MatthiasWM/NewtonROMReader/otg.cpp

/*
 * In this file in this order:
 * - usbhost.cpp
 * - ff.cpp
 */


#include "otg.h"

// ==== otg.cpp ==========================================================

int uhgogo;

char otgbufrd[512];
char otgbufwr[512];
void otgfill(char *buf, int pat);
int otgBlRead(int slot, int block, int pat);
int otgBlWrite(int slot,int block, int pat);
int otgBlTest(int slot, int n);
extern char otgbufrd[512];
extern char otgbufwr[512];

#ifdef USEFATFS
FATFS fatfs;
void otgFsRead(char *fname);
void otgFsWrite(char *s);
void otgFsLs(char *s);
#endif // USEFATFS

//  cmdServer()
//  read a command from Rs232
//  execute the command

extern void (*gpf_isr)(void);
#define CMDLINEFULL 80
char cmdline[CMDLINEFULL+2];
int cmdlinepp;
void
cmdServer()
{ char *s= cmdline;
  int i, j;
  if (cmdlinepp==0) memset(cmdline, 0, sizeof(cmdline));
  if (Serial.available()>0){
    i= Serial.read();
    if ((i>=' ')&& (cmdlinepp < CMDLINEFULL))
      cmdline[cmdlinepp++]= i;
    if ((i=='\n') && (cmdlinepp>0))
      cmdlinepp= CMDLINEFULL;
  }
  if (cmdlinepp< CMDLINEFULL)
    return;         // and loop
  printf("> %s\n", cmdline);
  cmdlinepp= 0;

  if (strcmp(s, "go")==0){        // go
    printf("start uh server\n");
    uhgogo= 1;
    return;
  }
  if (strncmp(s, "v=", 2)==0){        // v= <verbose>
    i= strtol(s+2, 0, 10);
    uhstate.verbose= i;
    printf("verbose=%d\n", i);
    return;
  }
  if (strncmp(s, "blrd ", 5)==0){       // blrd <lba>
    i= strtol(s+5, &s, 10);
    j= strtol(s, 0, 16);
    otgBlRead(0, i, j<=0? -1: j);
    return;
  }
  if (strncmp(s, "blwr ", 5)==0){       // blwr <lba> <pat>
    i= strtol(s+5, &s, 10);
    j= strtol(s, 0, 16);
    otgBlWrite(0, i, j);
    return;
  }
  if (strncmp(s, "bltst", 5)==0){       // bltst <cnt>
    i= strtol(s+5, &s, 10);
    otgBlTest(0, i);
    return;
  }
  if (strcmp(s, "u")==0){         // u
    uhDump();
    return;
  }
#ifdef USEFATFS
  if (strcmp(s, "ls")==0){        // ls
    otgFsLs(s+3);
    return;
  }
  if (strncmp(s, "rd ", 3)==0){       // rd <filename>
    otgFsRead(s+3);
    return;
  }
  if (strncmp(s, "wr ", 3)==0){     // wr <filename> <n> <pat>
    otgFsWrite(s+3);
    return;
  }
#endif // USEFATFS
  printf("ERROR unknown cmd <%s>\n", cmdline);
}


#define VERBOSE1 if (uhstate.verbose)
#define VERBOSE2 if (uhstate.verbose>1)

void
uhServer()
{ static u64 t0init;      // no more than 1 per 2s
  static int ostat= UHSTAT_NULL;
  static int fs=0;
  int st;
  if (ostat== UHSTAT_NULL)
    uhInit();     // init driver
  st= uhstate.state;
  if (st<UHSTAT_DEV)
    t0init= 0;
  if (st!=ostat)        // stat changed
    VERBOSE1 uhPrintState();
  if ((st>=UHSTAT_DEV) && (st<UHSTAT_READY) && ((millis()-t0init)>2000)){
    uhInit();     // silent
    fs= 0;
  t0init= millis();
  }
  if ((st>= UHSTAT_READY)&& (fs==0)){
#ifdef USEFATFS
    memset (&fatfs, 0, sizeof(fatfs));
    f_mount(0, &fatfs);
#endif // USEFATFS
    fs= 1;
  }
  ostat= st;
}


//   pattern  -2  no compare, no dump
//    -1  no compare, dump
//    0.. compare, dump if error
//   return <0  error
//      0 rd ok, compare error
//      >0  ok, compare ok
//      
void
otgfill(char *buf, int pat)
{ int i;
  for (i=0; i<512; i++, buf++)
    *buf= pat++;
}

int
otgBlRead(int slot, int block, int pat)
{ 
  (void)slot;
  int i;
  VERBOSE1 if (pat!=-2) printf("read %d %0x\n", block, pat==-1? 0: pat);
  otgfill(otgbufwr, pat);
  if ((i= mscReadBlock(block, otgbufrd))< 0){
    printf("read failed %d\n", i);
    return i;
  }
  if (memcmp(otgbufrd, otgbufwr, 512)==0){
    return 1;
  }
  if (pat>=0)
    printf("read %d %0x compare failed\n", block, pat);
  if (pat!=-2)
    dumphex(otgbufrd, 0, 512);
  if (pat>=0){
    printf("pattern: %d %d\n", block, pat);
    dumphex(otgbufwr, 0, 512);
  }
  return 0;
}


int
otgBlWrite(int slot,int block, int pat)
{ 
  (void)slot;
  int i;
  VERBOSE1 printf("write %d %0x\n", block, pat);
  otgfill(otgbufwr, pat);
  if ((i= mscWriteBlock( block, otgbufwr))!= 0){
    printf("write failed %d\n", i);
    return 0;
  }
  return 1;
}

const int otgdt[]= { 13,0x55, 177,0x33, 1333,0x12,  117,0x00, 888,0x88, 300, 0x33,
         73,0xCC, 155,0xAF, 1404,0xE2, 1488,0x99, 999,0xFF, 257, 0xA5,
    0 };
int
otgBlTest(int slot, int n)
{ const int *p;
  if (n<1) n=1;
  for (;n>0; n--){
    for (p= otgdt; *p>0; p+=2 )
      if (otgBlWrite(slot, *p, p[1]+n)==0)
        return 0;
    for (p= otgdt; *p>0; p+=2 )
      if (otgBlRead(slot, *p, p[1]+n)==0)
        return 0;
  }
  printf("Test finished ok\n");
  return 1;
}

#ifdef USEFATFS

void
otgFsLs(char *s)
{ DIR dir; int i; char at;
  FILINFO fin;
  char lfn[_MAX_LFN+1];
#if _USE_LFN
  fin.lfname= lfn;
  fin.lfsize= sizeof(lfn);
#endif
  if ((i=f_opendir(&dir, "/"))!=0){
    printf("ERROR f_opendir %d\n", i);
    return;
  }
  for (i=0; i<100; i++){
    memset(lfn, 0, sizeof(lfn));
    if (f_readdir(&dir, &fin)!=0)
      break;
    if (fin.fname[0]==0) break;   // problem f_readdir() !
    if (lfn[0]!=0)
      printf("< %-20s", lfn);
    else
      printf("< %-20s", fin.fname);
    at=' ';
    if (fin.fattrib&AM_DIR) at='/';
    printf(" %c %d\n", at, fin.fsize);
  }
  
}

void
otgFsRead(char *fname)
{ int i;
  FIL fd;
  char buf[80];
  if ((i=f_open(&fd, fname, FA_READ))!=0){
    printf("ERROR f_open <%s> %d\n", fname, i);
    return;
  }
  while (f_gets( buf, sizeof(buf), &fd)!=0){
    printf("< %s", buf);
  }
  printf("\nEOF\n", buf);
  f_close(&fd);
}

void
otgFsWrite(char *s)
{ int i, lmax;
  FIL fd;
  char *fname=s;
  char buf[80];
  while (*s>' ') s++;
  if (*s!=0) *s++= 0;
  lmax= strtol(s, &s, 10);
  while (*s==' ') s++;
  if (lmax<=0) lmax=10;
  if ((i=f_open(&fd, fname, FA_WRITE|FA_CREATE_ALWAYS))!=0){
    printf("ERROR f_open <%s> %d\n", fname, i);
    return;
  }
  for (i=1; i<= lmax; i++){
    sprintf(buf,"line %d ", i);
    f_puts(buf, &fd);
    f_puts(s, &fd);
    f_puts("\n", &fd);
  }
  f_close(&fd);
  printf("write %s %d lines done\n", fname, lmax);
}

#endif // USEFATFS

// +++ usbhost() driver integration

void
uhStatServer()        // display stat on LED
{
#if 0
  if (uhstate.state>= UHSTAT_READY)
    digitalWrite(13, HIGH);   // turn led on
  else  digitalWrite(13, LOW);    // turn led off
          PIOA->PIO_CODR= LEDBIT2;
  else  PIOA->PIO_SODR= LEDBIT2;
#endif
}

void
uhWaitMs(int n)
{
  uhStatServer();
  delay(n);
  uhStatServer();
}

void
uhSwitch()
{
  uhStatServer();
//  switch to other task
  uhStatServer();
}

#ifdef USEFATFS
#
// +++ fatfs integration

struct billstime {
  u32 sec:5,    // seconds/2 0-29
    min: 6,   // minutes 0-59
    hour: 5,  // hour 0-23 (gmt)
    day:5,    // dd 1-31
    month: 4, // MM 1-12
    year: 7;  // yyyy-1980
};

DWORD
get_fattime()
{ union {
    DWORD d;
    struct billstime b;
  } u;
  u.d= 0;
  u.b.year= 2017-1980;
  u.b.month= 7;
  u.b.day= 24;
  u.b.hour= 16;
  u.b.min= 44;
  return u.d;
}

#if _USE_LFN
WCHAR
ff_convert(WCHAR x, UINT mode)
{ return x;
}

WCHAR
ff_wtoupper(WCHAR x)
{ return x;
}
#endif // _USE_LFN

// +++ fatfs -> usbhost interface

//  ff -> usbhost interface

DSTATUS
disk_initialize (BYTE lun)
{
  if (uhstate.state== UHSTAT_READY)
    return RES_OK;
  return RES_ERROR;
}

DSTATUS
disk_status (BYTE lun)
{
  if (uhstate.state== UHSTAT_READY)
    return RES_OK;
  return RES_ERROR;
}

DRESULT
disk_read (BYTE lun, BYTE *buf, DWORD lba, BYTE cnt)
{ int i;
  for (;cnt>0; lba++, buf+=512, cnt--){
    VERBOSE2 printf("disk_read lba=%d\n", lba);
    if ((i=mscReadBlock(lba, (char *)buf))<0)
      return RES_ERROR;
  }
  return RES_OK;
}

DRESULT
disk_write (BYTE lun, const BYTE *buf, DWORD lba, BYTE cnt)
{ int i;
  for (;cnt>0; lba++, buf+=512, cnt--){
    VERBOSE2 printf("disk_write lba=%d\n", lba);
    if ((i=mscWriteBlock(lba, (char *)buf))<0)
      return RES_ERROR;
  }
  return RES_OK;
}

DRESULT
disk_ioctl (BYTE lun, BYTE cmd, void* p)
{
  VERBOSE1 printf("disk_ioctl %d\n", cmd);
  switch (cmd) {
  case GET_SECTOR_SIZE:
  case GET_BLOCK_SIZE:
      * ((DWORD *)p)= 512;
      return RES_OK;
  case GET_SECTOR_COUNT:
      * ((DWORD *)p)= uhstate.capacity;
      return RES_OK;
  case CTRL_SYNC:
      return RES_OK;
  }
  VERBOSE1 printf("ERROR disk_ioctl %d\n", cmd);
  return RES_ERROR;
}

#endif // USEFATFS


// +++ suppport and debug functions

void
dumphex(const char *p, u32 addr, int cnt)
{ int i; uchar c; u32 *pp;
  const char tohex[]="0123456789ABCDEF";
  for (;cnt >0; cnt-=16, p+=16, addr+=16) {
    printf("%08X:", addr);
    for (i=0; i<16; i++){
      c= p[i];
      if ((i%4)==0)
        printf(" ");
      if (i < cnt)
        printf("%c%c", tohex[(c>>4)&0xF], tohex[c&0xF]);
      else  printf("  ");
    }
    printf(" /");
    for (i=0; i<16; i++){
      c= p[i];
      if ((i < cnt)&& (c>=' ') && (c<0x7F))
        printf("%c", c);
      else  printf(" ");
    }
    printf("/");
#if 1
    if ((((u32)p)&0x3)==0){   // 32bit alligned
      pp= (u32*) p; 
      for (i=0; i<16; i+=4, pp++)
        if (i<cnt)
          printf(" %08X", *pp);
    }
#endif
    printf("\n");
  }
}



// ==== usbhost.cpp ======================================================

/*
This code is in the public domain.
Created by Andreas Meyer controlord/at/controlord/dot/fr
Version 201712  (dec 2017)
*/

//#include "duedue.h"
//#include "usbhost.h"

void uhSetState(int i);     // only down!
void uhSetStateUp(int i);   // down or up 1
void uhSetStateXXX(int i);
const char *uhStatAsc();
void uhInit();
void uhInitx(char *s);
void uhInitPipe(int pipe, int token);
void uhInitPipeToken(int pipe, int token);
void uhInitAllocDpram();
void uhInitPeriph();
int uhInitResetUsb(int n, int inix);
int  uhInitEnum();
void uhEnumSaveDescr(u8 *d);
void uhEnumPrintDescr(u8 *d, int tlng);
int uhEnumConfig(u8 *d, int tlng);
void uhResetDevEndpointIn();
const char * uhErrorAsc(int ecode);
int uhSendPipe(int pipe, u8 *buf, int lng);
int uhReceivePipe(int pipe, u8 *buf, int lng);
extern void udd_interrupt();
void uhInterrupt();
void uhInterruptPipe(int pipe);
extern void (*gpf_isr)(void);

void mscInit();
int mscTstUnitReady();
int mscInquiry();
int mscReadCapacity();
int mscRequestSense();
int mscReceiveWrapper(int pipe, u32 stall);
int mscReadBlock(u32 lba, char *buf);
int mscWriteBlock(u32 lba, char *buf);
const char *scsi2asc(int code);
void uhDumpx(int pipe, const char *pre, int destr);

int uhStepFrom, uhStepTo;
#define VERBOSE0      // severe internal errors, "can not happen"
#define VERBOSE1 if (uhstate.verbose)
#define VERBOSE2 if (uhstate.verbose>1)
#define VERBOSE3 if (uhstate.verbose>2)

// +++  usbhost, msc,  scsi ***********

// +++ usb host + enumeration

#define UHLOG if (0) uhramlog
void uhramlog(const char *fmt, ...);      // debug support

#define UHPIPE_CTRL 0
#define UHPIPE_IN 1
#define UHPIPE_OUT  2
#define UHPIPES   10      // just for arrays
//#define UOTGHS_DPRAM  0x20180000
#define UOTGHS_DPRAM  UOTGHS_RAM_ADDR

//struct _uhstate {
//  volatile int  state;    // off, enumeration, ready
//  u32 capacity;   // total number of blocks
//  u16 idVendor;   // enumeration
//  u16 idProduct;
//  u8  vendor_id[8+1]; 
//  u8  product_id[16+1];
//  u8  product_rev[4+1];
//  u16 maxPower;
//};
struct _uhstate uhstate;
  
struct _uhx {         // internals
  struct _cnt {
    u32 sof;      // count sof events
    u32   pipeint;
    u32 connect;
    u32 disconnect;
    u32 stall;
    u32 tout;
    u32 errs[10]; // -1...
    u32 mscErrors;  // signal msc rd/wr error
  } cnt;
  u8  *uhDmaStartaddress;
  char  *fifoaddr[UHPIPES];
  int devpipein;    // device endpoint
  int devpipeout;   // device endpoint
  int devpipeoutLng;    // endpoint max package size
  u32 msctag;
  struct _it {
    volatile u32 pipe;
    volatile u32 mask;
    volatile u32 isr;
    volatile int done;  // 0=waiting for, >0: ok, <0: UHERROR_
  } it;       // uhx.it.
} uhx;

const char *
uhStatAsc()
{ switch(uhstate.state){
  case UHSTAT_NULL: return "";
  case UHSTAT_NODEV:  return "NODEV";
  case UHSTAT_DEV:  return "DEV";
  case UHSTAT_ENUM: return "ENUM";
  case UHSTAT_READY:  return "READY";
  default:    return "??? stat unknown";
  }
}

#define UHERROR_NOTREADY -1
#define UHERROR_TIMEOUT -2
#define UHERROR_STALL -3    // not really an error
#define UHERROR_REPLY -4
#define UHERROR_INTERN -5
#define UHERROR_IO -6
#define UHTIMEOUT 1000    // ms
#define UHTIMEOUTSENSER 5000    // ms senserequest  ?????

const char *uhAscErrors[]= { "notready", "timeout", "stall", "reply",
              "intern", "io"};
const char *
uhErrorAsc(int ecode)
{ switch(ecode){
  default:    return "";
  case UHERROR_NOTREADY:  return "ERROR: NOT READY";
  case UHERROR_TIMEOUT: return "ERROR: TIMEOUT";
  case UHERROR_STALL: return "ERROR: STALL";
  case UHERROR_REPLY: return "ERROR: REPLY";
  case UHERROR_INTERN:  return "ERROR: INTERN";
  case UHERROR_IO:  return "ERROR: IO";
  }
}

// usb device setup request

typedef struct _usb_request {
  u8  urRequestType;
  u8  urRequest;
  u16 urValue;
  u16 urIndex;
  u16 urLeng;
} usb_request;
#define USBREQUESTLNG 8
#define urFill(t, rq, v, ix, lng) \
  memset(&ur, 0, sizeof(ur));\
  ur.urRequestType= t; \
  ur.urRequest= rq; \
  ur.urValue= v; \
  ur.urIndex= ix; \
  ur.urLeng= lng;

// urRequestType
#define  USB_REQ_DIR_OUT  (0<<7) //!< Host to device
#define  USB_REQ_DIR_IN   (1<<7) //!< Device to host

#define  USB_REQ_TYPE_STANDARD  (0<<5) //!< Standard request
//#define  USB_REQ_TYPE_CLASS (1<<5) //!< Class-specific request
//#define  USB_REQ_TYPE_VENDOR  (2<<5) //!< Vendor-specific request

#define  USB_REQ_RECIP_DEVICE (0<<0) //!< Recipient device
//#define  USB_REQ_RECIP_INTERFACE (1<<0) //!< Recipient interface
#define  USB_REQ_RECIP_ENDPOINT  (2<<0) //!< Recipient endpoint
//#define  USB_REQ_RECIP_OTHER  (3<<0) //!< Recipient other
//#define  USB_REQ_RECIP_MASK (0x1F) //!< Mask

// urRequest
//efine USB_REQ_GET_STATUS    0
#define USB_REQ_CLEAR_FEATURE   1
//efine USB_REQ_SET_FEATURE   3
#define USB_REQ_SET_ADDRESS   5
#define USB_REQ_GET_DESCRIPTOR    6
//efine USB_REQ_SET_DESCRIPTOR    7
//efine USB_REQ_GET_CONFIGURATION 8
#define USB_REQ_SET_CONFIGURATION 9
//efine USB_REQ_GET_INTERFACE   10
//efine USB_REQ_SET_INTERFACE   11
//efine USB_REQ_SYNCH_FRAME   12

#define USB_EP_FEATURE_HALT   0 //  endpoint feature


#define USB_DT_DEVICE  1
#define USB_DT_CONFIGURATION  2
#define USB_DT_INTERFACE  4
#define USB_DT_ENDPOINT 5

//  USB device descriptor s

typedef struct _usb_devdesr{    // devioce descr
  u8  bLength;    //  0:
  u8  bDescriptorType;  //  1:
  u16 bcdUSB;     //  2:
  u8  bDeviceClass;   //  4:
  u8  bDeviceSubClass;  //  5:
  u8  bDeviceProtocol;  //  6:
  u8  bMaxPacketSize0;  //  7:
  u16 idVendor;   //  8:
  u16 idProduct;    //  A:
  u16 bcdDevice;    //  C:
  u8  iManufacturer;    //  E:
  u8  iProduct;   //  F:
  u8  iSerialNumber;    // 10:
  u8  bNumConfigurations; // 11: total: 18 bytes
} usb_devdescr;

typedef struct {      // configuration decr
  u8  bLength;
  u8  bDescriptorType;
  u16 wTotalLength;
  u8  bNumInterfaces;
  u8  bConfigurationValue;
  u8  iConfiguration;
  u8  bmAttributes;   // 0x40= self powered
  u8  bMaxPower;    // *2mA   lng=9
  u8  stuff[46];    // 23= 1 interface(9) + 2 epdescr(7)
} usb_confdescr;
#define CONFDESCRLNG 9

typedef struct {      // interface descr.
  u8  bLength;
  u8  bDescriptorType;
  u8  bInterfaceNumber;
  u8  bAlternateSetting;
  u8  bNumEndpoints;
  u8  bInterfaceClass;  // need MSC_CLASS
  u8  bInterfaceSubClass;
  u8  bInterfaceProtocol;
  u8  iInterface;
} usb_ifacedescr;

#define MSC_CLASS 0x08
#define  MSC_SUBCLASS_TRANSPARENT   0x06
#define  MSC_PROTOCOL_BULK          0x50

typedef struct {      // endpoint descr
  u8  bLength;
  u8  bDescriptorType;
  u8  bEndpointAddress;
  u8  bmAttributes;
  u8  wMaxPacketSize[2];
  u8  bInterval;
} usb_epdescr;
#define  USB_EP_DIR_IN        0x80
#define  USB_EP_DIR_OUT       0x00

#define USB_EP_TYPE_BULK 2

void
uhSetState(int i)     // only down!
{ if (i< uhstate.state)
    uhstate.state= i; 
  uhStatServer();
}

void
uhSetStateUp(int i)     // down or up 1
{ if (i< uhstate.state)
    uhstate.state= i; 
  if (i== uhstate.state+1)
    uhstate.state= i; 
  uhStatServer();
}

void
uhSetStateXXX(int i)      // set uncondiotioned (debug only)
{ uhstate.state= i; 
  uhStatServer();
}

int
uhError(int e)
{ int i;
  i= -1-e;        // -1->0 -2->1 ...
  if ((i>=0) && (i<10)) uhx.cnt.errs[i]++;
  UHLOG("error %d", e);
//  uhSetState(sowhat);
//  set last error ?;
  return e;
}

void
uhPrintState()
{ const char *speed;
  switch ((UOTGHS->UOTGHS_SR & UOTGHS_SR_SPEED_Msk)>>UOTGHS_SR_SPEED_Pos){
    case 0: speed= "full"; break;
    case 1: speed= "high"; break;
    case 2: speed= "low" ; break;
    default: speed="???" ; break;
  }
  printf("%s %s speed",
    uhStatAsc(),  speed);
  if (uhstate.verbose)
    printf(" v=%d", uhstate.verbose);
  if (uhstate.state>= UHSTAT_READY)
    printf(" vendor= %04X %s product= %04X %s curr= %dmA"
      " mem= %dGB",
    uhstate.idVendor, uhstate.vendor_id, uhstate.idProduct,
          uhstate.product_id,
          uhstate.maxPower,
    (uhstate.capacity/2000+300)/1000);
  printf("\n");
}


//  uhInit():
//  uhInitPeriph()  init usb host       -> UHSTAT_NODEV
//  wait for dev to connect         -> UHSTAT_DEV
//  uhInitEnum()  enumeration phase     -> UHSTAT_ENUM
//  mscInit()   int msc/sci interface, get device infos -> UHSTAT_READY
//
// ATmel:
//  step1 0: reset
//  step2 11: 20ms
//  step3 32: reset
//  step4 43: 100ms
//  step5 143: get device descr
//  step6 143: 20ms
//  step7 163: reset
//  step8 174: 100ms
//  step9 274: set address 
//  step10 274: 20ms
//  step11 294: new adrress, get dev descriptor

void
uhInit()
{ uhInitx((char *)""); }

void
uhInitx(char *s)
{
  uhStepFrom= strtol(s, &s, 10);
  if (*s==',') s++;
  uhStepTo= strtol(s, &s, 10);
  if (uhStepTo<=0) uhStepTo= 9999;
  uhInitAllocDpram();
  if (uhstate.state== UHSTAT_NULL){
    uhSetStateUp(UHSTAT_NODEV);   // stat _NULL -> _NODEV
    uhInitPeriph();
    u64 t0;
    for (t0=millis(); millis()< (t0+500);){
      uhSwitch();
      if (uhstate.state== UHSTAT_DEV)
        break;
    }
    VERBOSE2 printf("%s dev after %d ms\n",
      uhstate.state== UHSTAT_DEV? "": "no", (int)(millis()-t0));
  }
  if (uhStepTo<3)         // uhin ,2 -> stop
    goto end;
  if (uhstate.state== UHSTAT_DEV)
    uhInitEnum();
  if (uhStepTo<100)       // uhin ,99 -> stop
    goto end;
  if (uhstate.state== UHSTAT_ENUM)
    mscInit();
    end:
  VERBOSE2 printf("uhInit status= %d %s\n", uhstate.state,  uhStatAsc());
}

// seems to be ok (?)
//  same70: PLL=600  HCLK=300  MCK=150MHz   
//  sam3x:  PLL=168  HCLK= 84  MCK= 84
//  UPLLCK = 480 MHz
#define  USBDIV (10-1)      // UPLLCK / 10 --> 48 MHz
void
usbclkInit(int on)
{ 
  (void)on;
  volatile Pmc *pmc= PMC;
  PMC->CKGR_UCKR= CKGR_UCKR_UPLLCOUNT(0x3Fu) | CKGR_UCKR_UPLLEN;
  while ( !(PMC->PMC_SR & PMC_SR_LOCKU) );
  pmc->PMC_USB= PMC_USB_USBDIV(USBDIV)|PMC_USB_USBS; // UPLLCK /10
//  pmc->PMC_SCER= PMC_SCER_USBCLK;           // enable usb clock
  pmc->PMC_SCER= PMC_SCER_UOTGCLK;          // enable usb clock NYI ???

}

void
uhInitPeriph()
{ volatile Uotghs *usb= UOTGHS;
  u64 t0;
  VERBOSE2 printf("uhInitPeriph\n");
#define UOTGVBOF (1<<10)
  PIOB->PIO_PER= UOTGVBOF;
  PIOB->PIO_OER= UOTGVBOF;
  PIOB->PIO_SODR= UOTGVBOF;   // ext-power-> usb-power

  usb->UOTGHS_CTRL =        // host mode, unfreeze
      UOTGHS_CTRL_USBE|   // enable usb
      UOTGHS_CTRL_VBUSHWC;
//NYI perClockEnable(ID_UOTGHS, 1);
  usbclkInit(1);
//NYI NVIC_SetPriority((IRQn_Type) ID_UOTGHS, 5);
//NYI NVIC_EnableIRQ((IRQn_Type) ID_UOTGHS);
  gpf_isr=  uhInterrupt;
  usb->UOTGHS_CTRL =        // host mode, unfreeze
      UOTGHS_CTRL_USBE|   // enable usb
      UOTGHS_CTRL_VBUSHWC;
  usb->UOTGHS_HSTCTRL= 0;
  for (t0=millis()+1000; t0>millis();){
    uhSwitch();
    if (usb->UOTGHS_SR& UOTGHS_SR_CLKUSABLE)
      goto uhp1;
  }
  VERBOSE0 printf("uhInitPerph failed (clk usable)\n");
  return;
   uhp1:
  usb->UOTGHS_HSTICR= 0x7F;     // clear all it
  usb->UOTGHS_SFR = UOTGHS_SFR_VBUSRQS;   // enable vbus (must)
  usb->UOTGHS_HSTIER=
    UOTGHS_HSTIER_DCONNIES|
    UOTGHS_HSTIER_DDISCIES|
    0; //  UOTGHS_HSTIER_HSOFIES; // remove SOF ???
}

#define XX 1  // normal delay timing

// atmel reset proc step3:

int
uhInitResetUsb(int n, int inix)         // reset usb
{ volatile Uotghs *usb= UOTGHS;
  u64 t0; int ret=0;
  u32 hstier= usb->UOTGHS_HSTIMR;
  uhInitPeriph();
  UHLOG("reset usb");
  usb->UOTGHS_HSTIDR= 0xFFFFFFFF;
  usb->UOTGHS_HSTCTRL= 0;
  usb->UOTGHS_HSTCTRL= UOTGHS_HSTCTRL_RESET;  // reset usb
  for (t0=millis(); millis()<t0+ 5000;){  // 500 !!!
    uhSwitch();
    if (usb->UOTGHS_HSTISR& UOTGHS_HSTISR_RSTI)
      goto uhp2;
  }
  VERBOSE1 printf("uhInitReset failed (reset %d)\n", n);
  ret= UHERROR_NOTREADY;
    uhp2:
  VERBOSE2 printf("reset in %d ms\n", (int)(millis()-t0));
  uhWaitMs(30*XX);
  usb->UOTGHS_HSTCTRL= 0;
  usb->UOTGHS_HSTICR= UOTGHS_HSTICR_RSTIC;
  usb->UOTGHS_HSTCTRL= UOTGHS_HSTCTRL_SOFE;   // sof enable, needed!
  uhWaitMs(20*XX);
  if (inix==0)
    goto ier;
  uhWaitMs(100*XX);
  usb->UOTGHS_HSTCTRL= UOTGHS_HSTCTRL_SOFE;   // sof enable, needed!
  uhWaitMs(3*XX);
  uhInitPipe(UHPIPE_CTRL, -1);
  uhWaitMs(10*XX);
    ier:
  usb->UOTGHS_HSTICR= 0x7F;     // clear all ints
  usb->UOTGHS_HSTIER= hstier;     // restore hst int mask
  return ret;
}


int
uhInitEnum()            // uhin
{ volatile Uotghs *usb= UOTGHS;
  int i, redocnt=0, lng=100;
  usb_request ur;
  usb_devdescr udev;
  usb_confdescr uconf;
  u8 confno;
  VERBOSE2 printf("uhInitEnum\n");
  switch (uhStepFrom){
  case 5: goto step5;       // uhin 5
  case 6: goto step6;
  case 7: goto step7;
  case 13: goto step13;
  }
  uhWaitMs(50*XX);        // essentiel needs this
  if ((i=uhInitResetUsb(1, 0))<0)     // reset usb
    return i;
  if ((i=uhInitResetUsb(2, 1))<0)     // reset usb
    return i;

  usb->UOTGHS_HSTADDR1= (0<<16)|(0<<8)|(0<<0);
  if (uhStepTo<= 5) return 0;     // uhin ,5
    step5:
  VERBOSE2 printf("Step5 get dev descr\n"); // step5 get devdescr
  VERBOSE3 uhDumpx(-1, "", 1);
  UHLOG("step5 get dev descr");
  urFill( USB_REQ_RECIP_DEVICE|USB_REQ_TYPE_STANDARD|USB_REQ_DIR_IN,
    USB_REQ_GET_DESCRIPTOR, 
    USB_DT_DEVICE<<8,
    0,
    8);
  if ((i=uhSendPipe(UHPIPE_CTRL, (u8 *)&ur, USBREQUESTLNG))<0) // step5
    return i;
  if (uhStepTo<= 6) return 0;     // uhin ,6
    step6:
  if ((i=uhReceivePipe(UHPIPE_CTRL, (u8 *)&udev, sizeof(udev)))<0)
    return i;
  if (uhStepTo<= 7) return 0;     // uhin ,7

  uhWaitMs(20*XX);
    step7:
  if ((i=uhInitResetUsb(3, 1))<0)     // reset usb step7
    return i;

  VERBOSE2 printf("Step9 set addr\n");    // step9 set address
  UHLOG("step9 set addr");
  urFill( USB_REQ_RECIP_DEVICE|USB_REQ_TYPE_STANDARD|USB_REQ_DIR_OUT,
    USB_REQ_SET_ADDRESS,    // set address
    1,        // new address
    0,
    0);

  if ((i=uhSendPipe(UHPIPE_CTRL, (u8 *)&ur, USBREQUESTLNG))<0)
    return i;
  if ((i=uhReceivePipe(UHPIPE_CTRL, 0, 0))<0)
    return i;
  uhWaitMs(20*XX);

  VERBOSE2 printf("Step11 get dev descr\n");  // step11 new ad, get dev descr
  UHLOG("step11 get dev descr");
  usb->UOTGHS_HSTADDR1= (1<<16)|(1<<8)|(1<<0);
  urFill( USB_REQ_RECIP_DEVICE|USB_REQ_TYPE_STANDARD|USB_REQ_DIR_IN,
    USB_REQ_GET_DESCRIPTOR,     // get descriptor
    USB_DT_DEVICE<<8,
    0,
    sizeof(usb_devdescr));
  if ((i=uhSendPipe(UHPIPE_CTRL, (u8 *)&ur, USBREQUESTLNG))<0)
    return i;
  if ((i=uhReceivePipe(UHPIPE_CTRL, (u8 *)&udev, sizeof(udev)))<0)
    return i;
  uhEnumSaveDescr((u8 *) &udev);
  VERBOSE2 uhEnumPrintDescr((u8 *) &udev, 0);

  VERBOSE2 printf("Step12 get conf descr\n"); // step12 get config descr
  UHLOG("step12 get conf descr");
  urFill( USB_REQ_RECIP_DEVICE|USB_REQ_TYPE_STANDARD|USB_REQ_DIR_IN,
    USB_REQ_GET_DESCRIPTOR,     // get descriptor
    USB_DT_CONFIGURATION<<8,
    0,
    CONFDESCRLNG);
  if ((i=uhSendPipe(UHPIPE_CTRL, (u8 *)&ur, USBREQUESTLNG))<0)
    return i;
  if ((i=uhReceivePipe(UHPIPE_CTRL, (u8 *)&uconf, CONFDESCRLNG))<0)
    return i;
  uhEnumSaveDescr((u8 *) &uconf);
  VERBOSE2 uhEnumPrintDescr((u8 *) &uconf, 0);
  confno= 1; 
  lng= uconf.wTotalLength;

  if (uhStepTo<= 13) return 0;      // uhin ,5
    step13:
  VERBOSE2 printf("Step13 get interf descr\n"); // step13 get interf. descr
  UHLOG("step13 get interf descr");
  if (lng>(int)sizeof(uconf)) lng= sizeof(uconf);
  urFill( USB_REQ_RECIP_DEVICE|USB_REQ_TYPE_STANDARD|USB_REQ_DIR_IN,
    USB_REQ_GET_DESCRIPTOR,     // get descriptor
    USB_DT_CONFIGURATION<<8|(confno-1),
    0,
    lng);
  if ((i=uhSendPipe(UHPIPE_CTRL, (u8 *)&ur, USBREQUESTLNG))<0)
    return i;
  memset(&uconf, 0, sizeof(uconf));
  if ((i=uhReceivePipe(UHPIPE_CTRL, (u8 *)&uconf, lng))<0){
    if (++redocnt<3) goto step13;   // for the sakeOf Lexar
    return i;
  }
  VERBOSE2 uhEnumPrintDescr((u8 *) &uconf, i);
  i=uhEnumConfig((u8 *) &uconf, i);
//  verify interface & endpoint descr, set confno
//  and reinit pipes 1,2
  uhInitPipe(UHPIPE_IN, -1);
  uhInitPipe(UHPIPE_OUT, -1);
  if (i>=0){
    VERBOSE2 printf("conf interface in pipe=%d endp=%d out pipe=%d"
             " endp=%d\n",
            UHPIPE_IN, uhx.devpipein, UHPIPE_OUT, uhx.devpipeout);
  } else VERBOSE2 printf("conf interface failed\n");

  VERBOSE2 printf("Step14\n");      // step14 enable dev config
  UHLOG("step14");

  urFill( USB_REQ_RECIP_DEVICE|USB_REQ_TYPE_STANDARD|USB_REQ_DIR_OUT,
    USB_REQ_SET_CONFIGURATION,    //  set config
    confno,
    0,
    0);
  if ((i=uhSendPipe(UHPIPE_CTRL, (u8 *)&ur, USBREQUESTLNG))<0)
    return i;
  if ((i=uhReceivePipe(UHPIPE_CTRL, 0, 0))<0)
    return i;

  uhSetStateUp(UHSTAT_ENUM);
  return 0;
}

void
uhResetDevEndpointIn()      // reset device endpoint in
{ int i;
  int ep= uhx.devpipein;      // device endpoint IN
  if (ep==0) ep= UHPIPE_IN;
  ep|= 0X80;
  usb_request ur;
  urFill( USB_REQ_RECIP_ENDPOINT|USB_REQ_TYPE_STANDARD|USB_REQ_DIR_OUT,
    USB_REQ_CLEAR_FEATURE,  
    USB_EP_FEATURE_HALT,
    ep,
    0);
  if ((i=uhSendPipe(UHPIPE_CTRL, (u8 *)&ur, USBREQUESTLNG))<0)
    return;
  if ((i=uhReceivePipe(UHPIPE_CTRL, 0, 0))<0)
    return;
  return;
}

void      // save descriptor device, config, -> uhstat
uhEnumSaveDescr(u8 *d)
{ 
  usb_devdescr *udev;
  usb_confdescr *uco;
  udev= (usb_devdescr *) d;
  uco= (usb_confdescr *) d;
  switch(d[1]){
  case USB_DT_DEVICE:
    uhstate.idVendor= udev->idVendor;
    uhstate.idProduct= udev->idProduct;
    break;
  case USB_DT_CONFIGURATION:
    uhstate.maxPower= uco->bMaxPower*2;
    break;
  }
}

void      // print descriptor device, config, interface, endpoint
uhEnumPrintDescr(u8 *d, int tlng)
{ 
  usb_devdescr *udev;
  usb_confdescr *uco;
  usb_ifacedescr *id;
  usb_epdescr *ep;
  int i, lng;
  char mclass[10], subcl[10], prot[10], eptype[0];
  more:
  lng= d[0];
  udev= (usb_devdescr *) d;
  uco= (usb_confdescr *) d;
  id=  (usb_ifacedescr *) d;
  ep=  (usb_epdescr *) d;
  switch(d[1]){
  case USB_DT_DEVICE:
    printf("dev descr devClass=%X devSubClass=%X devProt=%X"
      " idVendor=%04X idProduct=%04X\n",
      udev->bDeviceClass, udev->bDeviceSubClass,
            udev->bDeviceProtocol, udev->idVendor, udev->idProduct);
    break;
  case USB_DT_CONFIGURATION:
    printf("config descr tlng=%d interf=%d curr=%dmA\n",
           uco->wTotalLength, uco->bNumInterfaces, uco->bMaxPower*2);
    break;
  case USB_DT_INTERFACE:
    switch (id->bInterfaceClass){
    case MSC_CLASS: strcpy(mclass,"msc"); break;
    default: strcpy(mclass,"");
    }
    switch (id->bInterfaceSubClass){
    case MSC_SUBCLASS_TRANSPARENT: strcpy(subcl,"transp"); break;
    default: strcpy(subcl,"");
    }
    switch (id->bInterfaceProtocol){
    case MSC_PROTOCOL_BULK: strcpy(prot,"bulk"); break;
    default: strcpy(prot,"");
    }
    printf("interface desccr no=%d endps=%d class=%X(%s)"
             " subclass=%X(%s) prot=%d(%s)\n",
      id->bInterfaceNumber, id->bNumEndpoints,
            id->bInterfaceClass, mclass, id->bInterfaceSubClass,
            subcl, id->bInterfaceProtocol, prot);
    break;

  case USB_DT_ENDPOINT:
    switch (ep->bmAttributes){
    case USB_EP_TYPE_BULK: strcpy(eptype,"bulk"); break;
    default: strcpy(eptype,"");
    }
    i= (ep->wMaxPacketSize[1]<<8)|ep->wMaxPacketSize[0];
    printf("endpoint desccr attr=%d(%s) addr=%X"
             " packagesize=%d\n",
      ep->bmAttributes, eptype, ep->bEndpointAddress, i);
    break;
  default:
    printf("descr UNKNOWN typ=%d lng=%d\n", d[1], lng);
    break;
  }
  if ((lng>0) && ((tlng-= lng)>0)){
    d+= lng;
    goto more;
  }
}

int
uhEnumConfig(u8 *d, int tlng)
{ int got=0, i;
  usb_ifacedescr *id;
  usb_epdescr *ep;
  for (;tlng>0; tlng-= d[0], d+= d[0]){
    switch(d[1]){
    case USB_DT_INTERFACE:
      id= (usb_ifacedescr *) d;
      if ((id->bInterfaceClass   == MSC_CLASS)
      && (id->bInterfaceSubClass == MSC_SUBCLASS_TRANSPARENT)
      && (id->bInterfaceProtocol == MSC_PROTOCOL_BULK) )
        got=0x4;
      break;
    case USB_DT_ENDPOINT:
      ep= (usb_epdescr *) d;
      if (got==0)
              break;
      if (ep->bmAttributes != USB_EP_TYPE_BULK)
        break;
      i= (ep->wMaxPacketSize[1]<<8)|ep->wMaxPacketSize[0];
      if (ep->bEndpointAddress & USB_EP_DIR_IN) {
        uhx.devpipein = ep->bEndpointAddress&
                    ~USB_EP_DIR_IN;
        got|= 0x2;
      } else {
        uhx.devpipeout= ep->bEndpointAddress;
        uhx.devpipeoutLng= i;
        got|= 0x1;
      }
      break;
    }
  }
  return (got==0x7? 0: -1);
}


void
uhInitPipe(int pipe, int token)
{ volatile Uotghs *usb= UOTGHS;
  u32 type, size, devep;
  switch (pipe){
  case UHPIPE_CTRL:         // default?  cc 
  default:  type= UOTGHS_HSTPIPCFG_PTYPE_CTRL;
      if (token<0)
        token=  UOTGHS_HSTPIPCFG_PTOKEN_SETUP;
      size= UOTGHS_HSTPIPCFG_PSIZE_64_BYTE;
      devep= UHPIPE_CTRL;
      break;
  case UHPIPE_IN: if (token<0)
        token=  UOTGHS_HSTPIPCFG_PTOKEN_IN;
      if ((devep= uhx.devpipein)==0)
        devep= UHPIPE_IN;
      goto ptypeblk;
  case UHPIPE_OUT: if (token<0)
        token=  UOTGHS_HSTPIPCFG_PTOKEN_OUT;
      if ((devep= uhx.devpipeout)==0)
        devep= UHPIPE_OUT;
  ptypeblk: type= UOTGHS_HSTPIPCFG_PTYPE_BLK;
      size= UOTGHS_HSTPIPCFG_PSIZE_512_BYTE;
      break;
  }

  usb->UOTGHS_HSTPIP|= UOTGHS_HSTPIP_PEN0<<pipe;    // enable
  usb->UOTGHS_HSTPIP|= UOTGHS_HSTPIP_PRST0<<pipe;   // reset 
  usb->UOTGHS_HSTIDR= (UOTGHS_HSTIDR_PEP_0<<pipe);    // disable ints
  usb->UOTGHS_HSTPIPCFG[pipe]=        // config
            UOTGHS_HSTPIPCFG_PEPNUM(devep)|
      type|
      token|
      size|
      UOTGHS_HSTPIPCFG_PBK_1_BANK|
      UOTGHS_HSTPIPCFG_ALLOC;

  usb->UOTGHS_HSTPIP&= ~(UOTGHS_HSTPIP_PRST0<<pipe);  // stop reset
  usb->UOTGHS_HSTPIPIER[pipe]=        // enable ints
      UOTGHS_HSTPIPIER_PFREEZES|
      UOTGHS_HSTPIPIER_RXSTALLDES|
      UOTGHS_HSTPIPIER_PERRES;
  usb->UOTGHS_HSTPIPICR[pipe]= 0xF7;      // ack all ints
  usb->UOTGHS_HSTIER= (UOTGHS_HSTIER_PEP_0<<pipe);    // enable ints
}

void
uhInitPipeToken(int pipe, int token)
{
  uhInitPipe(pipe, token);
}

void
uhInitAllocDpram()
{
  char *dp= (char*)UOTGHS_DPRAM;
  uhx.fifoaddr[UHPIPE_CTRL]= dp;
  dp+= 64;        // PSIZE_64 see above
  uhx.fifoaddr[UHPIPE_IN]= dp;
  dp+= 512;       // PSIZE_512 see above
  uhx.fifoaddr[UHPIPE_OUT]= dp;
}


int
uhSendPipe(int pipe, u8 *buf, int lng)
{ volatile Uotghs *usb= UOTGHS;
  u64 t0;
  int ret= 0;
  uhInitPipeToken(pipe, UOTGHS_HSTPIPCFG_PTOKEN_SETUP);
  uhx.it.pipe= pipe;
  uhx.it.mask=  UOTGHS_HSTPIPISR_TXSTPI;
  uhx.it.done= 0;
  VERBOSE2 printf("uhSendPipe pipe=%d %08X:\n", pipe, (unsigned int)uhx.fifoaddr[pipe]);
  VERBOSE2 dumphex((char *)buf, (u32)buf, lng);
  VERBOSE3 uhDumpx(0, "->fifo", 0);
  memcpy(uhx.fifoaddr[pipe], buf, lng);   // fill fifo
  usb->UOTGHS_HSTPIPICR[pipe]= 0xF7;    // ack all ints -> FIFOCON=1
  usb->UOTGHS_HSTPIPIER[pipe]= UOTGHS_HSTPIPIER_TXSTPES;  // en txstp  int
  usb->UOTGHS_HSTPIPIDR[pipe]= UOTGHS_HSTPIPIDR_FIFOCONC; // FIFOCOn=0, start 
  usb->UOTGHS_HSTPIPIDR[pipe]= UOTGHS_HSTPIPIDR_PFREEZEC; // unfreeze pipe

  for (t0=millis()+UHTIMEOUT; ;){   // wait TXOUTI
    if (uhx.it.done)
      break;
    uhSwitch();
    if (millis()>=t0){
      VERBOSE1 printf("ERROR uhSendPipe timeout\n");
      ret= uhError(UHERROR_TIMEOUT);
      break;
    }
  }
  if ((uhstate.verbose>1) && (ret==0))
    printf("uhSendPipe ok intisr=%08X isr=%08X dma=%08X lng= %d(%x)\n",
      uhx.it.isr, (unsigned int)usb->UOTGHS_HSTPIPISR[pipe],
      0, lng, lng);
  if ((uhstate.verbose>0) && (ret!=0)){
    printf("uhSendPipe ERROR intisr=%08X lng= %d(%x)\n",
    uhx.it.isr, 0, lng);
    uhDumpx(pipe,0,1);
  }
  usb->UOTGHS_HSTPIPIDR[pipe]= UOTGHS_HSTPIPIDR_TXSTPEC;  // dis txstp int
  usb->UOTGHS_HSTPIPIER[pipe]= UOTGHS_HSTPIPIER_PFREEZES; // freeze pipe
  if (uhstate.state< UHSTAT_DEV) ret= UHERROR_NOTREADY;
  return ret;
}

//
// setup pipe, receive data, copie fifo->buf

int
uhReceivePipe(int pipe, u8 *buf, int lng)
{ volatile Uotghs *usb= UOTGHS;
  u32 dlng, isr;
  u64 t0;
  int ret= 0;
  uhInitPipeToken(pipe, UOTGHS_HSTPIPCFG_PTOKEN_IN);
  uhx.it.pipe= pipe;
  uhx.it.mask=  UOTGHS_HSTPIPISR_RXINI;
  uhx.it.done=  0;
  VERBOSE2 printf("uhReceivePipe pipe=%d\n", pipe);
//  VERBOSE2 uhDumpx(0, "<-rcvP", 0);
  usb->UOTGHS_HSTPIPIER[pipe]= UOTGHS_HSTPIPIER_RXINES; // en tr empty int
  usb->UOTGHS_HSTPIPIDR[pipe]= UOTGHS_HSTPIPIDR_FIFOCONC; // FIFOCOn=0, start 
  usb->UOTGHS_HSTPIPIDR[pipe]= UOTGHS_HSTPIPIDR_PFREEZEC; // unfreeze pipe

  for (t0=millis()+UHTIMEOUT; ;){
    if ((uhx.it.done) &&
      (usb->UOTGHS_HSTPIPIMR[pipe]& UOTGHS_HSTPIPIMR_PFREEZE))
      break;
    uhSwitch();
    if (millis()>=t0){
      VERBOSE1 printf("ERROR uhReceivePipe timeout\n");
      ret= uhError(UHERROR_TIMEOUT);
      break;
    }
  }
  isr= usb->UOTGHS_HSTPIPISR[pipe];
  dlng= isr>> UOTGHS_HSTPIPISR_PBYCT_Pos;
  memset(buf, 0, lng);
  memcpy(buf, uhx.fifoaddr[pipe], dlng<lng? dlng: lng);
  if ((uhstate.verbose>0) && ((uhstate.verbose>1)||(ret!=0))){
    printf("uhReceivePipe %s lng=%d(%X) ",
      ret==0? "ok": "error", dlng, dlng);
    uhDumpx(0,0,1);
  }
  VERBOSE2 dumphex((char *)buf, (u32)buf, dlng);
  usb->UOTGHS_HSTPIPICR[pipe]= 0xF7;      // ack all ints 
  usb->UOTGHS_HSTPIPIDR[pipe]= UOTGHS_HSTPIPIDR_RXINEC; // en tr empty int
  usb->UOTGHS_HSTPIPIER[pipe]= UOTGHS_HSTPIPIER_PFREEZES; // freeze pipe
  if (uhstate.state< UHSTAT_DEV) return UHERROR_NOTREADY;
  if (ret==0) ret= dlng;
  return ret;
}

void
uhDmaSetupIn(int pipe, u8 *buf, int lng)
{ volatile Uotghs *usb= UOTGHS;
  volatile UotghsHstdma *hs= & usb->UOTGHS_HSTDMA[pipe-1];
  u32 ctrl;
  uhx.uhDmaStartaddress= buf;
  hs->UOTGHS_HSTDMANXTDSC=0;
  hs->UOTGHS_HSTDMAADDRESS= (u32)buf;
  ctrl= UOTGHS_HSTDMACONTROL_CHANN_ENB;
  hs->UOTGHS_HSTDMACONTROL= (lng<<16)| ctrl;
}

int
uhDmaSetupOut(int pipe, u8 *buf, int lng)
{ volatile Uotghs *usb= UOTGHS;
  volatile UotghsHstdma *hs= & usb->UOTGHS_HSTDMA[pipe-1];
  u32 ctrl;
  int i;
  uhx.uhDmaStartaddress= buf;
  hs->UOTGHS_HSTDMANXTDSC=0;
  hs->UOTGHS_HSTDMAADDRESS= (u32)buf;
  ctrl= UOTGHS_HSTDMACONTROL_CHANN_ENB |
    UOTGHS_HSTDMACONTROL_END_B_EN;    // -> pipe
  hs->UOTGHS_HSTDMACONTROL= (lng<<16)| ctrl;
  for (i=0; i<1000; i++)
    if (hs->UOTGHS_HSTDMAADDRESS>= ((u32)uhx.uhDmaStartaddress+lng))
      break;
  if (i>=1000){
    VERBOSE1 printf("ERROR uhDmaSetupOut send data to fifo\n");
    return -1;
  }
  return 0;
}

u32
uhDmaEnd(int pipe)      // return length of last dma transfer
{ volatile Uotghs *usb= UOTGHS;
  volatile UotghsHstdma *hs= & usb->UOTGHS_HSTDMA[pipe-1];
  return hs->UOTGHS_HSTDMAADDRESS- (u32)uhx.uhDmaStartaddress;
}

//  setup pipe, setup dma, copy data->fifo, send data
int
uhSend(int pipe, u8 *buf, int lng)
{ volatile Uotghs *usb= UOTGHS;
  u32 dlng;
  u64 t0;
  int ret= 0;
  if (uhstate.verbose>1) {
    printf("uhSend pipe=%d: ", pipe);
    if (strncmp((char *)buf, "USBC", 4)==0)
      printf("%s", scsi2asc(buf[15])); 
    printf("\n");
    dumphex((char *)buf, (u32)buf, lng);
  }
    more:
  uhx.it.pipe= pipe;
  uhx.it.mask=  UOTGHS_HSTPIPISR_TXOUTI;
  uhx.it.done= 0;
  dlng= uhx.devpipeoutLng;
  if ((dlng==0)||(dlng>lng))
    dlng= lng;
  if (uhDmaSetupOut(pipe, buf, dlng)<0){      // fill fifo
      ret= uhError(UHERROR_INTERN);
      goto ex;
  }
  usb->UOTGHS_HSTPIPICR[pipe]= 0xF7;    // ack all ints -> FIFOCON=1
  usb->UOTGHS_HSTPIPIER[pipe]= UOTGHS_HSTPIPIER_TXOUTES;  // en tr empty int
  usb->UOTGHS_HSTPIPIDR[pipe]= UOTGHS_HSTPIPIDR_PFREEZEC; // unfreeze pipe
  usb->UOTGHS_HSTPIPIDR[pipe]= UOTGHS_HSTPIPIDR_FIFOCONC; // FIFOCOn=0, start 

  for (t0=millis()+UHTIMEOUT; uhx.it.done==0;){
    uhSwitch();
    if (millis()>=t0){
      VERBOSE1 printf("ERROR uhSend timeout\n");
      ret= uhError(UHERROR_TIMEOUT);
      break;
    }
  }
  dlng= uhDmaEnd(pipe);
  if ((dlng<=0) && (ret==0)) ret= uhError(UHERROR_INTERN);
  if ((uhstate.verbose>0) && ((uhstate.verbose>1)||(ret!=0)))
    printf("uhSend %s intisr=%08X isr=%08X dma=%08X lng= %d(%x)\n",
    ret==0? "ok": "error",
    uhx.it.isr, usb->UOTGHS_HSTPIPISR[pipe], 0, dlng, dlng);
  usb->UOTGHS_HSTPIPIER[pipe]= UOTGHS_HSTPIPIER_PFREEZES; // freeze pipe
  if (uhstate.state< UHSTAT_ENUM) ret= UHERROR_NOTREADY;
  if ((ret==0) && (dlng< lng)) {        // more
    buf+= dlng;
    lng-= dlng;
    goto more;
  }
    ex:
  return ret;
}


//  setup dma, pipe, receive data

int
uhReceive(int pipe, u8 *buf, int lng, int tout)
{ volatile Uotghs *usb= UOTGHS;
  u32 dlng;
  u64 t0;
  int ret= 0;
  u8 *cbuf= buf;
  int   clng= lng;
  memset(buf, 0x33, lng);
    more:
  uhx.it.pipe= pipe;
  uhx.it.mask=  UOTGHS_HSTPIPISR_RXINI;
  uhx.it.done=  0;
  VERBOSE2 printf("uhReceive pipe=%d\n", pipe);
//  usb->UOTGHS_HSTPIPICR[pipe]= 0xF7;    // ack all ints -> FIFOCON=1
  usb->UOTGHS_HSTPIPIER[pipe]= UOTGHS_HSTPIPIER_RXINES; // en tr empty int
  usb->UOTGHS_HSTPIPIDR[pipe]= UOTGHS_HSTPIPIDR_FIFOCONC; // FIFOCOn=0, start 
  usb->UOTGHS_HSTPIPIDR[pipe]= UOTGHS_HSTPIPIDR_PFREEZEC; // unfreeze pipe
  uhDmaSetupIn(pipe, cbuf, clng);

  for (t0=millis()+ tout; uhx.it.done==0;){
    uhSwitch();
    if (millis()>=t0){
      VERBOSE1 printf("ERROR uhReceive timeout\n");
      ret= uhError(UHERROR_TIMEOUT);
      break;
    }
  }
  if (uhx.it.done<0)
    ret= uhError(uhx.it.done);      // STALL
  dlng= uhDmaEnd(pipe);
  if ((uhstate.verbose>1) ||
            ((uhstate.verbose>1)&&(ret!=0)&&(ret!=UHERROR_STALL))){
    printf("uhReceive %s lng=%d(%X) intisr= ",
          ret==0?"ok":"error", dlng,dlng, uhx.it.isr);
    uhDumpx(0,0,1);
  }
  usb->UOTGHS_HSTPIPIDR[pipe]= UOTGHS_HSTPIPIDR_RXINEC; // en tr empty int
  usb->UOTGHS_HSTPIPIER[pipe]= UOTGHS_HSTPIPIER_PFREEZES; // freeze pipe
  if (uhstate.state< UHSTAT_ENUM) ret= UHERROR_NOTREADY;
  if ((ret==0) && (dlng< clng)) {       // more
    cbuf+= dlng;
    clng-= dlng;
    goto more;
  }
  VERBOSE2 dumphex((char *)buf, (u32)buf, lng);
  return ret;
}

void
uhConnect(int present, u32 isr)
{ static  u64 otic; static int ocnt; int v;
  if ((millis()-otic)>1000) ocnt=0;   // avoid >5 msg/s
  otic= millis();
  ocnt++;
  if (present){
    uhx.cnt.connect++;
    uhSetStateUp(UHSTAT_DEV);
    if (ocnt<5){
      UHLOG("dev con %08x", isr);
      VERBOSE2 printf("dev connected\n");
    }
  } else {
    v= uhstate.verbose;
    memset(&uhstate, 0, sizeof(uhstate));
    uhstate.verbose= v;
    uhx.cnt.disconnect++;
    uhSetStateUp(UHSTAT_NODEV);
    UOTGHS->UOTGHS_HSTCTRL= 0;  // host to idle state
            // for the sakeOf Toshiba
    if (ocnt< 5){
      UHLOG("dev discon %08x", isr);
      VERBOSE2 printf("dev disconnected\n");
    }
  }
}

void
uhInterrupt()
{ volatile Uotghs *usb= UOTGHS;
  u32 pipe, isr, imr;
  uhStatServer();
  isr= UOTGHS->UOTGHS_HSTISR;
  imr = UOTGHS->UOTGHS_HSTIMR;
  pipe= ctz(((isr & imr) >> 8) | (1 << 10));
  if (isr & UOTGHS_HSTISR_HSOFI){       // sof
    usb->UOTGHS_HSTICR= UOTGHS_HSTICR_HSOFIC;
    uhx.cnt.sof++;
    return;
  }
  VERBOSE2 printf(".");
  if (imr & isr & UOTGHS_HSTISR_DDISCI){      // disconnect
    usb->UOTGHS_HSTICR= UOTGHS_HSTICR_DDISCIC |
           UOTGHS_HSTICR_DCONNIC;

    uhConnect(0, isr);
    return;
  }
  if (imr & isr & UOTGHS_HSTISR_DCONNI){      // connect
    usb->UOTGHS_HSTICR= UOTGHS_HSTICR_DCONNIC|
           UOTGHS_HSTICR_DDISCIC;
    uhConnect(1, isr);
    return;
  }
  if (pipe <10){
    uhInterruptPipe(pipe);
    uhStatServer();
    return;
  }
  printf("ERROR unexpected usb host int isr=%08X imr=%08X\n", isr, imr);
  usb->UOTGHS_HSTICR= 0x7F;
}
    
void
uhInterruptPipe(int pipe)
{ volatile Uotghs *usb= UOTGHS;
  u32 isr, imr, err, ack;
  isr= usb->UOTGHS_HSTPIPISR[pipe];
  imr= usb->UOTGHS_HSTPIPIMR[pipe];
  err= usb->UOTGHS_HSTPIPERR[pipe];
  uhx.cnt.pipeint++;
  if ((uhx.it.pipe==pipe) && ((uhx.it.mask&isr)!=0)&& (uhx.it.done==0)){
    uhx.it.done= 1;
  endpipe:
    uhx.it.isr= isr;
    UHLOG("p%d: int %X isr=%08X", pipe, isr&imr, isr);
    ack= isr&uhx.it.mask;
    usb->UOTGHS_HSTPIPICR[pipe]= ack;   // ack int
    return;
  }
  if (isr&UOTGHS_HSTPIPISR_RXSTALLDI){
    VERBOSE2 uhDumpx(pipe,"ERROR usb pipe STALL", 0); // STALL
    uhx.cnt.stall++;
    if ((uhx.it.pipe==pipe) && (uhx.it.done==0)){
      uhx.it.done= UHERROR_STALL;
      goto endpipe;
    }
  } else  VERBOSE1 uhDumpx(pipe,"ERROR unexpected usb pipe int", 0);
  if (err!=0)
    usb->UOTGHS_HSTPIPERR[pipe]=0;
  UHLOG("p%d: int %X isr=%08X", pipe, isr&imr, isr);
  usb->UOTGHS_HSTPIPICR[pipe]= 0xF7;      // ack all
}

#if 0 // just an example, to handle host & dev drivers
void UOTGHS_Handler()
{
  if (UOTGHS->UOTGHS_CTRL& UOTGHS_CTRL_UIMOD)
    udd_interrupt();
  else  uhInterrupt();
}
#endif

const char *uhpiperr[]={ "0 datagl","1 datapid","2 pid","3 timeout","4 crc16", 0 };
const char *uhpipimr[]={ "0 rxin", "1 txout", "2 txstp", "3 perr", "4 naked",
      "5 overf", "6 rxstalld", "7 shortpck", 
      "12 nbusybk", "14 ficocon", "16 pdishdma", "17 pfreeze",
      "18 rstdt", 0};
const char *uhpipisr[]= { "0 rxin", "1 txout", "2 txstp", "3 perr", "4 naked",
      "5 overf", "6 rxstalld", "7 shortpack",
      "16 rwall", "18 cfgok", "12,2 nbusybk", "14,2 currbk",
            "20,12 pbyct",  0 };


char *
uhDumpBits(u32 reg, char *buf, const char **txt)
{ const char *t;
  char *s= buf;
  u32 msk, r2;;
  int i, cnt;
  for (cnt=0; *txt!=0; txt++) {
    t= *txt;
    i= strtol(t, (char **)&t, 10);
    if (*t==','){
      msk= strtol(t+1, (char **)&t, 10);
    } else  msk=1;
    msk= (1<<msk)-1;      // 1->1, 2->3, 3->7
    if (*t==' ')t++;
    if ((r2= ((reg>>i) & msk))!=0){
      if (cnt++>0)
        *s++=',';
      if (msk==1)
        s+= sprintf(s, "%s", t);
      else  s+= sprintf(s, "%s=%d", t, r2);
    }
  }
  *s= 0;
  return buf;
}

void
uhDump()
{ uhDumpx(-1,"",1);
}

void
uhDumpx(int pipe, const char *pre, int destr)       // debug only
{ volatile Uotghs *usb= UOTGHS;
  volatile Pmc *pmc = PMC;
  u32 sta, isr, imr, ad, err, cfg, pepnum;
  const char *ptoken;
  char imrbits[50];
  char isrbits[50];
  char errbits[50];
  int i, n;
  if (pre==0) pre="";
  ad= usb->UOTGHS_HSTADDR1;
  if (pipe<0) {
  uhPrintState();
  printf("%s usb clk ckgr_uckr=%08X pmc_sr=%08X usb=%08X scsr=%08X"
    " ctrl=%08X stat=%08X\n",
      pre, pmc->CKGR_UCKR, pmc->PMC_SR, pmc->PMC_USB, pmc->PMC_SCSR,
      usb->UOTGHS_CTRL, usb->UOTGHS_SR);
  printf("%s host ctrl=%08X isr=%08X imr=%08X pip=%08X\n",
    pre, usb->UOTGHS_HSTCTRL, usb->UOTGHS_HSTISR, usb->UOTGHS_HSTIMR,
      usb->UOTGHS_HSTPIP);
  printf("%s ints=%d sof=%d cnct=%d disc=%d stall=%d tout=%d", pre,
    uhx.cnt.pipeint, uhx.cnt.sof,
          uhx.cnt.connect, uhx.cnt.disconnect, uhx.cnt.stall, uhx.cnt.tout);
  for (i=0; i<6; i++) printf(" %s:%d", uhAscErrors[i], uhx.cnt.errs[i]);
  printf("\n");
  }
  for (n=0; n<=2; n++){
    if ((pipe>=0) && (pipe!=n))
      continue;
    imr= usb->UOTGHS_HSTPIPIMR[n];
    isr= usb->UOTGHS_HSTPIPISR[n];
    err= usb->UOTGHS_HSTPIPERR[n];
    uhDumpBits(imr, imrbits, uhpipimr);
    uhDumpBits(isr, isrbits, uhpipisr);
    uhDumpBits(err, errbits, uhpiperr);
    cfg= usb->UOTGHS_HSTPIPCFG[n];
    pepnum=  (cfg& UOTGHS_HSTPIPCFG_PEPNUM_Msk)>> UOTGHS_HSTPIPCFG_PEPNUM_Pos;
    switch (cfg& UOTGHS_HSTPIPCFG_PTOKEN_Msk){
      case UOTGHS_HSTPIPCFG_PTOKEN_IN:  ptoken="in "; break;
      case UOTGHS_HSTPIPCFG_PTOKEN_OUT: ptoken="out"; break;
      default:       ptoken="???"; break;
    }
    printf("%s pipe %d->%d %s ad=%d cfg=%05X imr=%06X isr=%08X err=%X",
      pre, n, pepnum, ptoken, (ad>>(8*n))&0x7F, cfg, imr, isr, err);
    if (n>0){
      printf(" dma addr=%08X ctrl=%04X",
        usb->UOTGHS_HSTDMA[n-1].UOTGHS_HSTDMAADDRESS,
        usb->UOTGHS_HSTDMA[n-1].UOTGHS_HSTDMACONTROL&0xFFFF);
      if (destr){
        sta= usb->UOTGHS_HSTDMA[n-1].UOTGHS_HSTDMASTATUS;
        printf(" cnt=%04X stat=%04X", sta>>16, sta& 0xFFFF);
      }
    }
    printf(" imr=%s isr=%s err=%s", imrbits, isrbits, errbits);
    printf("\n");
  }
  if (pipe<0)
  printf("%s dev pipe in=%d out=%d packagesz=%d\n", pre,
    uhx.devpipein, uhx.devpipeout, uhx.devpipeoutLng);
}

void
uhramlog(const char *fmt, ...)      // debug support
{
}

// +++ msc + scsi

// +++ msc wrapper
//  doc: usb mass storage class bulk-only transport: 5: command/data/status
//  little endian 
typedef struct _cbwrapper {   // msc command block wrapper
  char  cbwsig[4];    //  0: signature
  u32 cbwtag;     //  4: tag
  u32 cbwlng;     //  8: data transfer length
  u8  cbwflags;   //  C: flags
  u8  cbwlun;     //  D: dev logical unit number
  u8  cbwcblng;   //  E: length cbwcb
  u8  cbwcb[16];    //  F: cbwcb
} cbwrap;
#define CBWRAPLNG 31
#define CBWFLAGIN 0x80
#define CBWFLAGOUT 0x00

typedef struct _cswrapper {   // msc command status wrapper
  char  cswsig[4];    //  4: signature
  u32 cswtag;     //  8: tag
  u32 cswlng;     //  C: data residue
  u8  cswstatus;    //  D: status
} cswrap;
#define CSWRAPLNG 13

// +++ scsi commands
// big endian 
// doc: Usb Mass Storage Calls UFI Command spec
typedef struct _scsicmd {
  u8  a[12];
} scsicmd;
#define SCSICMDLNG  12

#define SCSI_TESTUNITREADY  0x00
#define SCSI_REQUESTSENSE 0x03
#define SCSI_INQUIRY    0x12
//efine SCSI_MODESENSE    0x1A  
#define SCSI_READCAPACITY 0x25
#define SCSI_READBLOCK    0x28
#define SCSI_WRITEBLOCK   0x2A

typedef struct _scsiInquiry {   // should be in msc scsi, needed
  u8  type;     //  0:per. data type
#define SCSI_TYPE_CONNECTED 0
  u8  flags1;
#define SCSI_FLAG1_REMOVABLE  0x80
  u8  version;
  u8  flags3;
  u8  addlng;     //  add. lng
  u8  flags5;
  u8  flags6;
  u8  flags7;
  u8  vendor_id[8];   //  8: vendor
  u8  product_id[16];   // 10: product
  u8  product_rev[4];   // 20: revision
} scsiInquiry;
#define SCSI_INQUIRYLNG   0x24

typedef struct _scsiCapacity{
  u32 lastlba;    // 0: last lba 
  u32 lastlbalng;   // 0: last lba lng
} scsiCapacity;
#define SCSI_CAPACITYLNG  0x8

typedef struct _scsiSense {
  u8  ecode;
  u8  res1;
  u8  sensekey;
  u8  info[4];
  u8  addlng;
  u8  res2[4];
  u8  asc;      // add sense code
  u8  ascq;     // add sense code quqlif
  u8  res3[3];
} scsiSense;
#define SCSI_SENSELNG  17

int mscReceive(u8 *cbwcb, int cbwcblng, u8 *buf, int datalng, int tout);
int mscSend(u8 *cbwcb, int cbwcblng, u8 *buf, int datalng);
int mscSendWrapper(int pipe, u8 *cbwcb, int flags, int cbwcblng, int datalng);
int mscReceiveWrapper(int pipe, u32 stall);

const char
*scsi2asc(int code)
{ switch(code){
  case  SCSI_TESTUNITREADY: return "test unit ready";
  case  SCSI_REQUESTSENSE:  return "request sense";
  case  SCSI_INQUIRY:   return "inquiry";
//  case  SCSI_MODESENSE:   return "mode sense";
  case  SCSI_READCAPACITY:  return "read capacity";
  case  SCSI_READBLOCK:   return "read block";
  case  SCSI_WRITEBLOCK:    return "write block";
  }
  return "";
}


//       getcapa
//        stall-> ResetDevEndpointIn, read stat, again
void
mscInit()
{ int ret, i1, i2=-1, i3=-1;

  if (uhstate.state< UHSTAT_ENUM) return; //  UHERROR_NOTREADY;
  VERBOSE2 printf("uhInit mscInit\n");
  VERBOSE3 uhDumpx(-1, "mscinit", 1);
  i1=ret= mscInquiry();
  if (ret>=0)
    i2=ret=mscRequestSense();
  if (ret>=0)
    i3=ret= mscReadCapacity();
  if (ret>=0) uhSetStateUp(UHSTAT_READY);
  if (uhstate.state!= UHSTAT_READY)
    VERBOSE1 printf("ERROR  ");
  VERBOSE2 printf("stat=%d %s inquiry= %d reqSense=%d getcapa=%d\n",
            uhstate.state, uhStatAsc(), i1, i2, i3);
}

int
mscTstUnitReady()
{ scsicmd sc;
  int i;
  if (uhstate.state< UHSTAT_ENUM) return UHERROR_NOTREADY;
  memset(&sc, 0, sizeof(sc));
  sc.a[0]= SCSI_TESTUNITREADY;
  i= mscReceive((u8 *)&sc, SCSICMDLNG, 0, 0, UHTIMEOUT);
  return i;
}

int
mscInquiry()
{ scsicmd sc;
  scsiInquiry inq;
  int i, rcnt=2;
    redo:
  if (uhstate.state< UHSTAT_ENUM) return UHERROR_NOTREADY;
  memset(&sc, 0, sizeof(sc));
  sc.a[0]= SCSI_INQUIRY;
  sc.a[4]= SCSI_INQUIRYLNG; 
  i= mscReceive((u8 *)&sc, SCSICMDLNG, (u8*)&inq, SCSI_INQUIRYLNG, UHTIMEOUT);
  if ((i== UHERROR_STALL)&&(--rcnt>0)){
    uhWaitMs(100);
    goto redo;
  }
  if (i<0)
    memset(&inq, 0, sizeof(inq));
  memcpy(uhstate.vendor_id, inq.vendor_id, sizeof(inq.vendor_id));
  memcpy(uhstate.product_id, inq.product_id, sizeof(inq.product_id));
  memcpy(uhstate.product_rev, inq.product_rev, sizeof(inq.product_rev));
  return i;
}

int
mscReadCapacity()
{ scsicmd sc;
  scsiCapacity cap;
  int i, capa, rcnt= 3;
    redo:
  if (uhstate.state< UHSTAT_ENUM) return UHERROR_NOTREADY;
  memset(&sc, 0, sizeof(sc));
  sc.a[0]= SCSI_READCAPACITY;
  uhstate.capacity= 0;
  i= mscReceive((u8 *)&sc, SCSICMDLNG, (u8*)&cap, SCSI_CAPACITYLNG,UHTIMEOUT);
  if ((i== UHERROR_STALL)&&(--rcnt>0)){
    uhWaitMs(100);
    goto redo;
  }
  if (i<0) return i;
  capa=  __builtin_bswap32(cap.lastlba);
  uhstate.capacity= capa;
  VERBOSE2 printf("capacity=%d blocks %d MB\n", capa,  capa/2000);
  return 0;
}


int
mscRequestSense()
{ scsicmd sc;
  scsiSense ss;
  int i, rcnt= 3;
    redo:
  if (uhstate.state< UHSTAT_ENUM) return UHERROR_NOTREADY;
  memset(&sc, 0, sizeof(sc));
  sc.a[0]= SCSI_REQUESTSENSE;
  sc.a[4]= SCSI_SENSELNG;
  uhstate.capacity= 0;
  i= mscReceive((u8 *)&sc, SCSICMDLNG, (u8*)&ss, SCSI_SENSELNG,
            UHTIMEOUTSENSER);
  if ((i== UHERROR_STALL)&&(--rcnt>0)){
    uhWaitMs(100);
    goto redo;
  }
  if (i<0)
    return i;
  VERBOSE2 printf("request sense: error=%02X key=%02x asc=%02x ascq=%02x\n",
      ss.ecode, ss.sensekey, ss.asc, ss.ascq);
  return 0;
}

void
little2big32(u8 *to, u32 from)    // conver little<->big endian
{ u8* fr= (u8*)&from;
  to[0]= fr[3];     
  to[1]= fr[2];
  to[2]= fr[1];
  to[3]= fr[0];
}

int
mscReadBlock(u32 lba, char *buf)
{ scsicmd sc;
  int i;
#if 0
  if (!ISALIGN32(buf)){
    VERBOSE1 printf("ERROR mscReadBlock alignment \n");
    return UHERROR_IO;
   }
#endif
  if (uhstate.state< UHSTAT_READY) return UHERROR_NOTREADY;
  if (lba>= uhstate.capacity) return UHERROR_IO;
  memset(&sc, 0, sizeof(sc));
  sc.a[0]= SCSI_READBLOCK;
  little2big32(&sc.a[2], lba);
  sc.a[8]= 1;       //big endian
  if ((i= mscReceive((u8 *) &sc, SCSICMDLNG, (u8*) buf, 512, UHTIMEOUT))<0){
    uhx.cnt.mscErrors++;
    uhSetState(UHSTAT_DEV);   // set down to reinit
    return i;
  }
  VERBOSE2 printf("mscReadBlock %d ok\n", lba);
  return 0;
}


int
mscWriteBlock(u32 lba, char *buf)
{ scsicmd sc;
  int i;
#if 0
  if (!ISALIGN32(buf)){
    VERBOSE1 printf("ERROR mscWriteBlock alignment \n");
    return UHERROR_IO;
  }
#endif
  if (uhstate.state< UHSTAT_READY) return UHERROR_NOTREADY;
  if (lba>= uhstate.capacity) return UHERROR_IO;
  memset(&sc, 0, sizeof(sc));
  sc.a[0]= SCSI_WRITEBLOCK;
  little2big32(&sc.a[2], lba);
  sc.a[8]= 1;       //big endian
  if ((i= mscSend((u8*) &sc, SCSICMDLNG, (u8*) buf, 512))<0){
    uhx.cnt.mscErrors++;
    uhSetState(UHSTAT_DEV);   // set down to reinit
    return i;
  }
  VERBOSE2 printf("mscWriteBlock %d ok\n", lba);
  return 0;
}

//  send msc wrapper
//  receive data
//  receive wrapper
int
mscReceive(u8 *cbwcb, int cbwcblng, u8 *buf, int datalng, int tout)
{ int i, i2;
  if ((i=mscSendWrapper(UHPIPE_OUT, cbwcb, CBWFLAGIN, cbwcblng, datalng))<0)
    return i;
  if (datalng>0){
    UHLOG("uhReceive:");
    i=uhReceive(UHPIPE_IN, buf, datalng, tout);
    UHLOG("mscReceive end");
    if (i==UHERROR_STALL)
      uhResetDevEndpointIn();
  }
  i2= mscReceiveWrapper(UHPIPE_IN, i);
  if (i<0) return i; else return i2;
}

//  send msc wrapper
//  send data
//  receive wrapper
int
mscSend(u8 *cbwcb, int cbwcblng, u8 *buf, int datalng)
{ int i;
  if ((i=mscSendWrapper(UHPIPE_OUT, cbwcb, CBWFLAGOUT, cbwcblng, datalng))<0)
    return i;
  UHLOG("uhSend:");
  if ((i=uhSend(UHPIPE_OUT, buf, datalng))<0)
    return i;
  UHLOG("mscReceive end");
  return mscReceiveWrapper(UHPIPE_IN, 0);
}

//  send msc wrapper
int
mscSendWrapper(int pipe, u8 *cbwcb, int flags, int cbwcblng, int datalng)
{ cbwrap w;
  UHLOG("Sendwrap:");
  memset(&w, 0, sizeof(w));
  memcpy(w.cbwsig, "USBC", 4);
  w.cbwtag= ++uhx.msctag;
  w.cbwlng=  datalng;
  w.cbwflags=  flags;
  w.cbwlun=  0;
  w.cbwcblng=  cbwcblng;
  memcpy(w.cbwcb, cbwcb, cbwcblng);
  return uhSend(pipe, (u8*) &w, CBWRAPLNG);
}


//  receive msc wrapper
//  verify wrapper
int
mscReceiveWrapper(int pipe, u32 stall)
{ int i;
  cswrap csw;
  UHLOG("Recwrap:");
  if ((i=uhReceive(pipe, (u8 *)&csw, CSWRAPLNG, UHTIMEOUT))<0)
    return i;
  if (memcmp(csw.cswsig,"USBS", 4)!=0){
    VERBOSE1 printf("ERROR mscReceiveWrap bad reply frame: sig\n");
    return uhError(UHERROR_REPLY);
  }
  if (csw.cswtag!= uhx.msctag){
    VERBOSE1 printf("ERROR mscReceiveWrap bad reply frame: tag %d %d\n",
        uhx.msctag, csw.cswtag);
    return uhError(UHERROR_REPLY);
  }
  if (csw.cswstatus!=0){
    if ((uhstate.verbose>1) ||
              ((uhstate.verbose>0) && (stall!= UHERROR_STALL)))
    printf("ERROR mscReceiveWrap bad reply state=%02X\n",
                csw.cswstatus);
    return uhError(UHERROR_REPLY);
  }
  return 0;
}

// ==== ff.cpp ===========================================================

/*----------------------------------------------------------------------------/
/  FatFs - FAT file system module  R0.09                  (C)ChaN, 2011
/-----------------------------------------------------------------------------/
/ FatFs module is a generic FAT file system module for small embedded systems.
/ This is a free software that opened for education, research and commercial
/ developments under license policy of following terms.
/
/  Copyright (C) 2011, ChaN, all right reserved.
/
/ * The FatFs module is a free software and there is NO WARRANTY.
/ * No restriction on use. You can use, modify and redistribute it for
/   personal, non-profit or commercial products UNDER YOUR RESPONSIBILITY.
/ * Redistributions of source code must retain the above copyright notice.
/
/-----------------------------------------------------------------------------/
/ Feb 26,'06 R0.00  Prototype.
/
/ Apr 29,'06 R0.01  First stable version.
/
/ Jun 01,'06 R0.02  Added FAT12 support.
/                   Removed unbuffered mode.
/                   Fixed a problem on small (<32M) partition.
/ Jun 10,'06 R0.02a Added a configuration option (_FS_MINIMUM).
/
/ Sep 22,'06 R0.03  Added f_rename().
/                   Changed option _FS_MINIMUM to _FS_MINIMIZE.
/ Dec 11,'06 R0.03a Improved cluster scan algorithm to write files fast.
/                   Fixed f_mkdir() creates incorrect directory on FAT32.
/
/ Feb 04,'07 R0.04  Supported multiple drive system.
/                   Changed some interfaces for multiple drive system.
/                   Changed f_mountdrv() to f_mount().
/                   Added f_mkfs().
/ Apr 01,'07 R0.04a Supported multiple partitions on a physical drive.
/                   Added a capability of extending file size to f_lseek().
/                   Added minimization level 3.
/                   Fixed an endian sensitive code in f_mkfs().
/ May 05,'07 R0.04b Added a configuration option _USE_NTFLAG.
/                   Added FSInfo support.
/                   Fixed DBCS name can result FR_INVALID_NAME.
/                   Fixed short seek (<= csize) collapses the file object.
/
/ Aug 25,'07 R0.05  Changed arguments of f_read(), f_write() and f_mkfs().
/                   Fixed f_mkfs() on FAT32 creates incorrect FSInfo.
/                   Fixed f_mkdir() on FAT32 creates incorrect directory.
/ Feb 03,'08 R0.05a Added f_truncate() and f_utime().
/                   Fixed off by one error at FAT sub-type determination.
/                   Fixed btr in f_read() can be mistruncated.
/                   Fixed cached sector is not flushed when create and close without write.
/
/ Apr 01,'08 R0.06  Added fputc(), fputs(), fprintf() and fgets().
/                   Improved performance of f_lseek() on moving to the same or following cluster.
/
/ Apr 01,'09 R0.07  Merged Tiny-FatFs as a configuration option. (_FS_TINY)
/                   Added long file name feature.
/                   Added multiple code page feature.
/                   Added re-entrancy for multitask operation.
/                   Added auto cluster size selection to f_mkfs().
/                   Added rewind option to f_readdir().
/                   Changed result code of critical errors.
/                   Renamed string functions to avoid name collision.
/ Apr 14,'09 R0.07a Separated out OS dependent code on reentrant cfg.
/                   Added multiple sector size feature.
/ Jun 21,'09 R0.07c Fixed f_unlink() can return FR_OK on error.
/                   Fixed wrong cache control in f_lseek().
/                   Added relative path feature.
/                   Added f_chdir() and f_chdrive().
/                   Added proper case conversion to extended char.
/ Nov 03,'09 R0.07e Separated out configuration options from ff.h to ffconf.h.
/                   Fixed f_unlink() fails to remove a sub-dir on _FS_RPATH.
/                   Fixed name matching error on the 13 char boundary.
/                   Added a configuration option, _LFN_UNICODE.
/                   Changed f_readdir() to return the SFN with always upper case on non-LFN cfg.
/
/ May 15,'10 R0.08  Added a memory configuration option. (_USE_LFN = 3)
/                   Added file lock feature. (_FS_SHARE)
/                   Added fast seek feature. (_USE_FASTSEEK)
/                   Changed some types on the API, XCHAR->TCHAR.
/                   Changed fname member in the FILINFO structure on Unicode cfg.
/                   String functions support UTF-8 encoding files on Unicode cfg.
/ Aug 16,'10 R0.08a Added f_getcwd(). (_FS_RPATH = 2)
/                   Added sector erase feature. (_USE_ERASE)
/                   Moved file lock semaphore table from fs object to the bss.
/                   Fixed a wrong directory entry is created on non-LFN cfg when the given name contains ';'.
/                   Fixed f_mkfs() creates wrong FAT32 volume.
/ Jan 15,'11 R0.08b Fast seek feature is also applied to f_read() and f_write().
/                   f_lseek() reports required table size on creating CLMP.
/                   Extended format syntax of f_printf function.
/                   Ignores duplicated directory separators in given path names.
/
/ Sep 06,'11 R0.09  f_mkfs() supports multiple partition to finish the multiple partition feature.
/                   Added f_fdisk(). (_MULTI_PARTITION = 2)
/---------------------------------------------------------------------------*/

//#include "ff.h"      /* FatFs configurations and declarations */
//#include "diskio.h"   /* Declarations of low level disk I/O functions */

/**
 * \defgroup thirdparty_fatfs_group FatFS file system service
 *
 * Service of FatFS file system. This service provides a generic FAT file
 * system module for the ASF systems.
 *
 * @{
 */
 
/*--------------------------------------------------------------------------

   Module Private Definitions

---------------------------------------------------------------------------*/

#if _FATFS != 6502  /* Revision ID */
#error Wrong include file (ff.h).
#endif


/* Definitions on sector size */
#if _MAX_SS != 512 && _MAX_SS != 1024 && _MAX_SS != 2048 && _MAX_SS != 4096
#error Wrong sector size.
#endif
#if _MAX_SS != 512
#define SS(fs)  ((fs)->ssize) /* Variable sector size */
#else
#define SS(fs)  512U      /* Fixed sector size */
#endif


/* Reentrancy related */
#if _FS_REENTRANT
#if _USE_LFN == 1
#error Static LFN work area must not be used in re-entrant configuration.
#endif
#define ENTER_FF(fs)    { if (!lock_fs(fs)) return FR_TIMEOUT; }
#define LEAVE_FF(fs, res) { unlock_fs(fs, res); return res; }
#else
#define ENTER_FF(fs)
#define LEAVE_FF(fs, res) return res
#endif

#define ABORT(fs, res)    { fp->flag |= FA__ERROR; LEAVE_FF(fs, res); }


/* File shareing feature */
#if _FS_SHARE
#if _FS_READONLY
#error _FS_SHARE must be 0 on read-only cfg.
#endif
typedef struct {
  FATFS *fs;        /* File ID 1, volume (NULL:blank entry) */
  DWORD clu;        /* File ID 2, directory */
  WORD idx;       /* File ID 3, directory index */
  WORD ctr;       /* File open counter, 0:none, 0x01..0xFF:read open count, 0x100:write mode */
} FILESEM;
#endif


/* Misc definitions */
#define LD_CLUST(dir) (((DWORD)LD_WORD(dir+DIR_FstClusHI)<<16) | LD_WORD(dir+DIR_FstClusLO))
#define ST_CLUST(dir,cl) {ST_WORD(dir+DIR_FstClusLO, cl); ST_WORD(dir+DIR_FstClusHI, (DWORD)cl>>16);}


/* DBCS code ranges and SBCS extend char conversion table */

#if _CODE_PAGE == 932 /* Japanese Shift-JIS */
#define _DF1S 0x81  /* DBC 1st byte range 1 start */
#define _DF1E 0x9F  /* DBC 1st byte range 1 end */
#define _DF2S 0xE0  /* DBC 1st byte range 2 start */
#define _DF2E 0xFC  /* DBC 1st byte range 2 end */
#define _DS1S 0x40  /* DBC 2nd byte range 1 start */
#define _DS1E 0x7E  /* DBC 2nd byte range 1 end */
#define _DS2S 0x80  /* DBC 2nd byte range 2 start */
#define _DS2E 0xFC  /* DBC 2nd byte range 2 end */

#elif _CODE_PAGE == 936 /* Simplified Chinese GBK */
#define _DF1S 0x81
#define _DF1E 0xFE
#define _DS1S 0x40
#define _DS1E 0x7E
#define _DS2S 0x80
#define _DS2E 0xFE

#elif _CODE_PAGE == 949 /* Korean */
#define _DF1S 0x81
#define _DF1E 0xFE
#define _DS1S 0x41
#define _DS1E 0x5A
#define _DS2S 0x61
#define _DS2E 0x7A
#define _DS3S 0x81
#define _DS3E 0xFE

#elif _CODE_PAGE == 950 /* Traditional Chinese Big5 */
#define _DF1S 0x81
#define _DF1E 0xFE
#define _DS1S 0x40
#define _DS1E 0x7E
#define _DS2S 0xA1
#define _DS2E 0xFE

#elif _CODE_PAGE == 437 /* U.S. (OEM) */
#define _DF1S 0
#define _EXCVT {0x80,0x9A,0x90,0x41,0x8E,0x41,0x8F,0x80,0x45,0x45,0x45,0x49,0x49,0x49,0x8E,0x8F,0x90,0x92,0x92,0x4F,0x99,0x4F,0x55,0x55,0x59,0x99,0x9A,0x9B,0x9C,0x9D,0x9E,0x9F, \
        0x41,0x49,0x4F,0x55,0xA5,0xA5,0xA6,0xA7,0xA8,0xA9,0xAA,0xAB,0xAC,0x21,0xAE,0xAF,0xB0,0xB1,0xB2,0xB3,0xB4,0xB5,0xB6,0xB7,0xB8,0xB9,0xBA,0xBB,0xBC,0xBD,0xBE,0xBF, \
        0xC0,0xC1,0xC2,0xC3,0xC4,0xC5,0xC6,0xC7,0xC8,0xC9,0xCA,0xCB,0xCC,0xCD,0xCE,0xCF,0xD0,0xD1,0xD2,0xD3,0xD4,0xD5,0xD6,0xD7,0xD8,0xD9,0xDA,0xDB,0xDC,0xDD,0xDE,0xDF, \
        0xE0,0xE1,0xE2,0xE3,0xE4,0xE5,0xE6,0xE7,0xE8,0xE9,0xEA,0xEB,0xEC,0xED,0xEE,0xEF,0xF0,0xF1,0xF2,0xF3,0xF4,0xF5,0xF6,0xF7,0xF8,0xF9,0xFA,0xFB,0xFC,0xFD,0xFE,0xFF}

#elif _CODE_PAGE == 720 /* Arabic (OEM) */
#define _DF1S 0
#define _EXCVT {0x80,0x81,0x45,0x41,0x84,0x41,0x86,0x43,0x45,0x45,0x45,0x49,0x49,0x8D,0x8E,0x8F,0x90,0x92,0x92,0x93,0x94,0x95,0x49,0x49,0x98,0x99,0x9A,0x9B,0x9C,0x9D,0x9E,0x9F, \
        0xA0,0xA1,0xA2,0xA3,0xA4,0xA5,0xA6,0xA7,0xA8,0xA9,0xAA,0xAB,0xAC,0xAD,0xAE,0xAF,0xB0,0xB1,0xB2,0xB3,0xB4,0xB5,0xB6,0xB7,0xB8,0xB9,0xBA,0xBB,0xBC,0xBD,0xBE,0xBF, \
        0xC0,0xC1,0xC2,0xC3,0xC4,0xC5,0xC6,0xC7,0xC8,0xC9,0xCA,0xCB,0xCC,0xCD,0xCE,0xCF,0xD0,0xD1,0xD2,0xD3,0xD4,0xD5,0xD6,0xD7,0xD8,0xD9,0xDA,0xDB,0xDC,0xDD,0xDE,0xDF, \
        0xE0,0xE1,0xE2,0xE3,0xE4,0xE5,0xE6,0xE7,0xE8,0xE9,0xEA,0xEB,0xEC,0xED,0xEE,0xEF,0xF0,0xF1,0xF2,0xF3,0xF4,0xF5,0xF6,0xF7,0xF8,0xF9,0xFA,0xFB,0xFC,0xFD,0xFE,0xFF}

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
#else     /* Two 2nd byte areas */
#define IsDBCS2(c)  (((BYTE)(c) >= _DS1S && (BYTE)(c) <= _DS1E) || ((BYTE)(c) >= _DS2S && (BYTE)(c) <= _DS2E))
#endif

#else     /* Code page is SBCS */

#define IsDBCS1(c)  0
#define IsDBCS2(c)  0

#endif /* _DF1S */


/* Name status flags */
#define NS      11    /* Index of name status byte in fn[] */
#define NS_LOSS   0x01  /* Out of 8.3 format */
#define NS_LFN    0x02  /* Force to create LFN entry */
#define NS_LAST   0x04  /* Last segment */
#define NS_BODY   0x08  /* Lower case flag (body) */
#define NS_EXT    0x10  /* Lower case flag (ext) */
#define NS_DOT    0x20  /* Dot entry */


/* FAT sub-type boundaries */
/* Note that the FAT spec by Microsoft says 4085 but Windows works with 4087! */
#define MIN_FAT16 4086  /* Minimum number of clusters for FAT16 */
#define MIN_FAT32 65526 /* Minimum number of clusters for FAT32 */


/* FatFs refers the members in the FAT structures as byte array instead of
/ structure member because the structure is not binary compatible between
/ different platforms */

#define BS_jmpBoot      0 /* Jump instruction (3) */
#define BS_OEMName      3 /* OEM name (8) */
#define BPB_BytsPerSec    11  /* Sector size [byte] (2) */
#define BPB_SecPerClus    13  /* Cluster size [sector] (1) */
#define BPB_RsvdSecCnt    14  /* Size of reserved area [sector] (2) */
#define BPB_NumFATs     16  /* Number of FAT copies (1) */
#define BPB_RootEntCnt    17  /* Number of root dir entries for FAT12/16 (2) */
#define BPB_TotSec16    19  /* Volume size [sector] (2) */
#define BPB_Media     21  /* Media descriptor (1) */
#define BPB_FATSz16     22  /* FAT size [sector] (2) */
#define BPB_SecPerTrk   24  /* Track size [sector] (2) */
#define BPB_NumHeads    26  /* Number of heads (2) */
#define BPB_HiddSec     28  /* Number of special hidden sectors (4) */
#define BPB_TotSec32    32  /* Volume size [sector] (4) */
#define BS_DrvNum     36  /* Physical drive number (2) */
#define BS_BootSig      38  /* Extended boot signature (1) */
#define BS_VolID      39  /* Volume serial number (4) */
#define BS_VolLab     43  /* Volume label (8) */
#define BS_FilSysType   54  /* File system type (1) */
#define BPB_FATSz32     36  /* FAT size [sector] (4) */
#define BPB_ExtFlags    40  /* Extended flags (2) */
#define BPB_FSVer     42  /* File system version (2) */
#define BPB_RootClus    44  /* Root dir first cluster (4) */
#define BPB_FSInfo      48  /* Offset of FSInfo sector (2) */
#define BPB_BkBootSec   50  /* Offset of backup boot sectot (2) */
#define BS_DrvNum32     64  /* Physical drive number (2) */
#define BS_BootSig32    66  /* Extended boot signature (1) */
#define BS_VolID32      67  /* Volume serial number (4) */
#define BS_VolLab32     71  /* Volume label (8) */
#define BS_FilSysType32   82  /* File system type (1) */
#define FSI_LeadSig     0 /* FSI: Leading signature (4) */
#define FSI_StrucSig    484 /* FSI: Structure signature (4) */
#define FSI_Free_Count    488 /* FSI: Number of free clusters (4) */
#define FSI_Nxt_Free    492 /* FSI: Last allocated cluster (4) */
#define MBR_Table     446 /* MBR: Partition table offset (2) */
#define SZ_PTE        16  /* MBR: Size of a partition table entry */
#define BS_55AA       510 /* Boot sector signature (2) */

#define DIR_Name      0 /* Short file name (11) */
#define DIR_Attr      11  /* Attribute (1) */
#define DIR_NTres     12  /* NT flag (1) */
#define DIR_CrtTime     14  /* Created time (2) */
#define DIR_CrtDate     16  /* Created date (2) */
#define DIR_FstClusHI   20  /* Higher 16-bit of first cluster (2) */
#define DIR_WrtTime     22  /* Modified time (2) */
#define DIR_WrtDate     24  /* Modified date (2) */
#define DIR_FstClusLO   26  /* Lower 16-bit of first cluster (2) */
#define DIR_FileSize    28  /* File size (4) */
#define LDIR_Ord      0 /* LFN entry order and LLE flag (1) */
#define LDIR_Attr     11  /* LFN attribute (1) */
#define LDIR_Type     12  /* LFN type (1) */
#define LDIR_Chksum     13  /* Sum of corresponding SFN entry */
#define LDIR_FstClusLO    26  /* Filled by zero (0) */
#define SZ_DIR        32    /* Size of a directory entry */
#define LLE         0x40  /* Last long entry flag in LDIR_Ord */
#define DDE         0xE5  /* Deleted directory enrty mark in DIR_Name[0] */
#define NDDE        0x05  /* Replacement of a character collides with DDE */


/*------------------------------------------------------------*/
/* Module private work area                                   */
/*------------------------------------------------------------*/
/* Note that uninitialized variables with static duration are
/  zeroed/nulled at start-up. If not, the compiler or start-up
/  routine is out of ANSI-C standard.
*/

#if _VOLUMES
static
FATFS *FatFs[_VOLUMES]; /* Pointer to the file system objects (logical drives) */
#else
#error Number of volumes must not be 0.
#endif

static
WORD Fsid;        /* File system mount ID */

#if _FS_RPATH
static
BYTE CurrVol;     /* Current drive */
#endif

#if _FS_SHARE
static
FILESEM Files[_FS_SHARE]; /* File lock semaphores */
#endif

#if _USE_LFN == 0     /* No LFN feature */
#define DEF_NAMEBUF     BYTE sfn[12]
#define INIT_BUF(dobj)    (dobj).fn = sfn
#define FREE_BUF()

#elif _USE_LFN == 1     /* LFN feature with static working buffer */
static WCHAR LfnBuf[_MAX_LFN+1];
#define DEF_NAMEBUF     BYTE sfn[12]
#define INIT_BUF(dobj)    { (dobj).fn = sfn; (dobj).lfn = LfnBuf; }
#define FREE_BUF()

#elif _USE_LFN == 2     /* LFN feature with dynamic working buffer on the stack */
#define DEF_NAMEBUF     BYTE sfn[12]; WCHAR lbuf[_MAX_LFN+1]
#define INIT_BUF(dobj)    { (dobj).fn = sfn; (dobj).lfn = lbuf; }
#define FREE_BUF()

#elif _USE_LFN == 3     /* LFN feature with dynamic working buffer on the heap */
#define DEF_NAMEBUF     BYTE sfn[12]; WCHAR *lfn
#define INIT_BUF(dobj)    { lfn = ff_memalloc((_MAX_LFN + 1) * 2); \
                if (!lfn) LEAVE_FF((dobj).fs, FR_NOT_ENOUGH_CORE); \
                (dobj).lfn = lfn; (dobj).fn = sfn; }
#define FREE_BUF()      ff_memfree(lfn)

#else
#error Wrong LFN configuration.
#endif




/*--------------------------------------------------------------------------

   Module Private Functions

---------------------------------------------------------------------------*/


/*-----------------------------------------------------------------------*/
/* String functions                                                      */
/*-----------------------------------------------------------------------*/

/* Copy memory to memory */
static
void mem_cpy (void* dst, const void* src, UINT cnt) {
  BYTE *d = (BYTE*)dst;
  const BYTE *s = (const BYTE*)src;

#if _WORD_ACCESS == 1
  while (cnt >= sizeof(int)) {
    *(int*)d = *(int*)s;
    d += sizeof(int); s += sizeof(int);
    cnt -= sizeof(int);
  }
#endif
  while (cnt--)
    *d++ = *s++;
}

/* Fill memory */
static
void mem_set (void* dst, int val, UINT cnt) {
  BYTE *d = (BYTE*)dst;

  while (cnt--)
    *d++ = (BYTE)val;
}

/* Compare memory to memory */
static
int mem_cmp (const void* dst, const void* src, UINT cnt) {
  const BYTE *d = (const BYTE *)dst, *s = (const BYTE *)src;
  int r = 0;

  while (cnt-- && (r = *d++ - *s++) == 0) ;
  return r;
}

/* Check if chr is contained in the string */
static
int chk_chr (const char* str, int chr) {
  while (*str && *str != chr) str++;
  return *str;
}



/*-----------------------------------------------------------------------*/
/* Request/Release grant to access the volume                            */
/*-----------------------------------------------------------------------*/
#if _FS_REENTRANT

static
int lock_fs (
  FATFS *fs   /* File system object */
)
{
  return ff_req_grant(fs->sobj);
}


static
void unlock_fs (
  FATFS *fs,    /* File system object */
  FRESULT res   /* Result code to be returned */
)
{
  if (res != FR_NOT_ENABLED &&
    res != FR_INVALID_DRIVE &&
    res != FR_INVALID_OBJECT &&
    res != FR_TIMEOUT) {
    ff_rel_grant(fs->sobj);
  }
}
#endif



/*-----------------------------------------------------------------------*/
/* File shareing control functions                                       */
/*-----------------------------------------------------------------------*/
#if _FS_SHARE

static
FRESULT chk_lock (  /* Check if the file can be accessed */
  DIR* dj,    /* Directory object pointing the file to be checked */
  int acc     /* Desired access (0:Read, 1:Write, 2:Delete/Rename) */
)
{
  UINT i, be;

  /* Search file semaphore table */
  for (i = be = 0; i < _FS_SHARE; i++) {
    if (Files[i].fs) {  /* Existing entry */
      if (Files[i].fs == dj->fs &&    /* Check if the file matched with an open file */
        Files[i].clu == dj->sclust &&
        Files[i].idx == dj->index) break;
    } else {      /* Blank entry */
      be++;
    }
  }
  if (i == _FS_SHARE) /* The file is not opened */
    return (be || acc == 2) ? FR_OK : FR_TOO_MANY_OPEN_FILES; /* Is there a blank entry for new file? */

  /* The file has been opened. Reject any open against writing file and all write mode open */
  return (acc || Files[i].ctr == 0x100) ? FR_LOCKED : FR_OK;
}


static
int enq_lock (void) /* Check if an entry is available for a new file */
{
  UINT i;

  for (i = 0; i < _FS_SHARE && Files[i].fs; i++) ;
  return (i == _FS_SHARE) ? 0 : 1;
}


static
UINT inc_lock ( /* Increment file open counter and returns its index (0:int error) */
  DIR* dj,  /* Directory object pointing the file to register or increment */
  int acc   /* Desired access mode (0:Read, !0:Write) */
)
{
  UINT i;


  for (i = 0; i < _FS_SHARE; i++) { /* Find the file */
    if (Files[i].fs == dj->fs &&
      Files[i].clu == dj->sclust &&
      Files[i].idx == dj->index) break;
  }

  if (i == _FS_SHARE) {       /* Not opened. Register it as new. */
    for (i = 0; i < _FS_SHARE && Files[i].fs; i++) ;
    if (i == _FS_SHARE) return 0; /* No space to register (int err) */
    Files[i].fs = dj->fs;
    Files[i].clu = dj->sclust;
    Files[i].idx = dj->index;
    Files[i].ctr = 0;
  }

  if (acc && Files[i].ctr) return 0;  /* Access violation (int err) */

  Files[i].ctr = acc ? 0x100 : Files[i].ctr + 1;  /* Set semaphore value */

  return i + 1;
}


static
FRESULT dec_lock (  /* Decrement file open counter */
  UINT i      /* Semaphore index */
)
{
  WORD n;
  FRESULT res;


  if (--i < _FS_SHARE) {
    n = Files[i].ctr;
    if (n == 0x100) n = 0;
    if (n) n--;
    Files[i].ctr = n;
    if (!n) Files[i].fs = 0;
    res = FR_OK;
  } else {
    res = FR_INT_ERR;
  }
  return res;
}


static
void clear_lock ( /* Clear lock entries of the volume */
  FATFS *fs
)
{
  UINT i;

  for (i = 0; i < _FS_SHARE; i++) {
    if (Files[i].fs == fs) Files[i].fs = 0;
  }
}
#endif



/*-----------------------------------------------------------------------*/
/* Change window offset                                                  */
/*-----------------------------------------------------------------------*/

static
FRESULT move_window (
  FATFS *fs,    /* File system object */
  DWORD sector  /* Sector number to make appearance in the fs->win[] */
)         /* Move to zero only writes back dirty window */
{
  DWORD wsect;


  wsect = fs->winsect;
  if (wsect != sector) {  /* Changed current window */
#if !_FS_READONLY
    if (fs->wflag) {  /* Write back dirty window if needed */
      if (disk_write(fs->drv, fs->win, wsect, 1) != RES_OK)
        return FR_DISK_ERR;
      fs->wflag = 0;
      if (wsect < (fs->fatbase + fs->fsize)) {  /* In FAT area */
        BYTE nf;
        for (nf = fs->n_fats; nf > 1; nf--) { /* Reflect the change to all FAT copies */
          wsect += fs->fsize;
          disk_write(fs->drv, fs->win, wsect, 1);
        }
      }
    }
#endif
    if (sector) {
      if (disk_read(fs->drv, fs->win, sector, 1) != RES_OK)
        return FR_DISK_ERR;
      fs->winsect = sector;
    }
  }

  return FR_OK;
}




/*-----------------------------------------------------------------------*/
/* Clean-up cached data                                                  */
/*-----------------------------------------------------------------------*/
#if !_FS_READONLY
static
FRESULT sync (  /* FR_OK: successful, FR_DISK_ERR: failed */
  FATFS *fs /* File system object */
)
{
  FRESULT res;


  res = move_window(fs, 0);
  if (res == FR_OK) {
    /* Update FSInfo sector if needed */
    if (fs->fs_type == FS_FAT32 && fs->fsi_flag) {
      fs->winsect = 0;
      /* Create FSInfo structure */
      mem_set(fs->win, 0, 512);
      ST_WORD(fs->win+BS_55AA, 0xAA55);
      ST_DWORD(fs->win+FSI_LeadSig, 0x41615252);
      ST_DWORD(fs->win+FSI_StrucSig, 0x61417272);
      ST_DWORD(fs->win+FSI_Free_Count, fs->free_clust);
      ST_DWORD(fs->win+FSI_Nxt_Free, fs->last_clust);
      /* Write it into the FSInfo sector */
      disk_write(fs->drv, fs->win, fs->fsi_sector, 1);
      fs->fsi_flag = 0;
    }
    /* Make sure that no pending write process in the physical drive */
    if (disk_ioctl(fs->drv, CTRL_SYNC, 0) != RES_OK)
      res = FR_DISK_ERR;
  }

  return res;
}
#endif




/*-----------------------------------------------------------------------*/
/* Get sector# from cluster#                                             */
/*-----------------------------------------------------------------------*/


static DWORD clust2sect ( /* !=0: Sector number, 0: Failed - invalid cluster# */
  FATFS *fs,    /* File system object */
  DWORD clst    /* Cluster# to be converted */
)
{
  clst -= 2;
  if (clst >= (fs->n_fatent - 2)) return 0;   /* Invalid cluster# */
  return clst * fs->csize + fs->database;
}




/*-----------------------------------------------------------------------*/
/* FAT access - Read value of a FAT entry                                */
/*-----------------------------------------------------------------------*/


static DWORD get_fat (  /* 0xFFFFFFFF:Disk error, 1:Internal error, Else:Cluster status */
  FATFS *fs,  /* File system object */
  DWORD clst  /* Cluster# to get the link information */
)
{
  UINT wc, bc;
  BYTE *p;


  if (clst < 2 || clst >= fs->n_fatent) /* Chack range */
    return 1;

  switch (fs->fs_type) {
  case FS_FAT12 :
    bc = (UINT)clst; bc += bc / 2;
    if (move_window(fs, fs->fatbase + (bc / SS(fs)))) break;
    wc = fs->win[bc % SS(fs)]; bc++;
    if (move_window(fs, fs->fatbase + (bc / SS(fs)))) break;
    wc |= fs->win[bc % SS(fs)] << 8;
    return (clst & 1) ? (wc >> 4) : (wc & 0xFFF);

  case FS_FAT16 :
    if (move_window(fs, fs->fatbase + (clst / (SS(fs) / 2)))) break;
    p = &fs->win[clst * 2 % SS(fs)];
    return LD_WORD(p);

  case FS_FAT32 :
    if (move_window(fs, fs->fatbase + (clst / (SS(fs) / 4)))) break;
    p = &fs->win[clst * 4 % SS(fs)];
    return LD_DWORD(p) & 0x0FFFFFFF;
  }

  return 0xFFFFFFFF;  /* An error occurred at the disk I/O layer */
}




/*-----------------------------------------------------------------------*/
/* FAT access - Change value of a FAT entry                              */
/*-----------------------------------------------------------------------*/
#if !_FS_READONLY

static FRESULT put_fat (
  FATFS *fs,  /* File system object */
  DWORD clst, /* Cluster# to be changed in range of 2 to fs->n_fatent - 1 */
  DWORD val /* New value to mark the cluster */
)
{
  UINT bc;
  BYTE *p;
  FRESULT res;


  if (clst < 2 || clst >= fs->n_fatent) { /* Check range */
    res = FR_INT_ERR;

  } else {
    switch (fs->fs_type) {
    case FS_FAT12 :
      bc = clst; bc += bc / 2;
      res = move_window(fs, fs->fatbase + (bc / SS(fs)));
      if (res != FR_OK) break;
      p = &fs->win[bc % SS(fs)];
      *p = (clst & 1) ? ((*p & 0x0F) | ((BYTE)val << 4)) : (BYTE)val;
      bc++;
      fs->wflag = 1;
      res = move_window(fs, fs->fatbase + (bc / SS(fs)));
      if (res != FR_OK) break;
      p = &fs->win[bc % SS(fs)];
      *p = (clst & 1) ? (BYTE)(val >> 4) : ((*p & 0xF0) | ((BYTE)(val >> 8) & 0x0F));
      break;

    case FS_FAT16 :
      res = move_window(fs, fs->fatbase + (clst / (SS(fs) / 2)));
      if (res != FR_OK) break;
      p = &fs->win[clst * 2 % SS(fs)];
      ST_WORD(p, (WORD)val);
      break;

    case FS_FAT32 :
      res = move_window(fs, fs->fatbase + (clst / (SS(fs) / 4)));
      if (res != FR_OK) break;
      p = &fs->win[clst * 4 % SS(fs)];
      val |= LD_DWORD(p) & 0xF0000000;
      ST_DWORD(p, val);
      break;

    default :
      res = FR_INT_ERR;
    }
    fs->wflag = 1;
  }

  return res;
}
#endif /* !_FS_READONLY */




/*-----------------------------------------------------------------------*/
/* FAT handling - Remove a cluster chain                                 */
/*-----------------------------------------------------------------------*/
#if !_FS_READONLY
static
FRESULT remove_chain (
  FATFS *fs,      /* File system object */
  DWORD clst      /* Cluster# to remove a chain from */
)
{
  FRESULT res;
  DWORD nxt;
#if _USE_ERASE
  DWORD scl = clst, ecl = clst, resion[2];
#endif

  if (clst < 2 || clst >= fs->n_fatent) { /* Check range */
    res = FR_INT_ERR;

  } else {
    res = FR_OK;
    while (clst < fs->n_fatent) {     /* Not a last link? */
      nxt = get_fat(fs, clst);      /* Get cluster status */
      if (nxt == 0) break;        /* Empty cluster? */
      if (nxt == 1) { res = FR_INT_ERR; break; }  /* Internal error? */
      if (nxt == 0xFFFFFFFF) { res = FR_DISK_ERR; break; }  /* Disk error? */
      res = put_fat(fs, clst, 0);     /* Mark the cluster "empty" */
      if (res != FR_OK) break;
      if (fs->free_clust != 0xFFFFFFFF) { /* Update FSInfo */
        fs->free_clust++;
        fs->fsi_flag = 1;
      }
#if _USE_ERASE
      if (ecl + 1 == nxt) { /* Next cluster is contiguous */
        ecl = nxt;
      } else {        /* End of contiguous clusters */ 
        resion[0] = clust2sect(fs, scl);          /* Start sector */
        resion[1] = clust2sect(fs, ecl) + fs->csize - 1;  /* End sector */
        disk_ioctl(fs->drv, CTRL_ERASE_SECTOR, resion);   /* Erase the block */
        scl = ecl = nxt;
      }
#endif
      clst = nxt; /* Next cluster */
    }
  }

  return res;
}
#endif




/*-----------------------------------------------------------------------*/
/* FAT handling - Stretch or Create a cluster chain                      */
/*-----------------------------------------------------------------------*/
#if !_FS_READONLY
static
DWORD create_chain (  /* 0:No free cluster, 1:Internal error, 0xFFFFFFFF:Disk error, >=2:New cluster# */
  FATFS *fs,      /* File system object */
  DWORD clst      /* Cluster# to stretch. 0 means create a new chain. */
)
{
  DWORD cs, ncl, scl;
  FRESULT res;


  if (clst == 0) {    /* Create a new chain */
    scl = fs->last_clust;     /* Get suggested start point */
    if (!scl || scl >= fs->n_fatent) scl = 1;
  }
  else {          /* Stretch the current chain */
    cs = get_fat(fs, clst);     /* Check the cluster status */
    if (cs < 2) return 1;     /* It is an invalid cluster */
    if (cs < fs->n_fatent) return cs; /* It is already followed by next cluster */
    scl = clst;
  }

  ncl = scl;        /* Start cluster */
  for (;;) {
    ncl++;              /* Next cluster */
    if (ncl >= fs->n_fatent) {    /* Wrap around */
      ncl = 2;
      if (ncl > scl) return 0;  /* No free cluster */
    }
    cs = get_fat(fs, ncl);      /* Get the cluster status */
    if (cs == 0) break;       /* Found a free cluster */
    if (cs == 0xFFFFFFFF || cs == 1)/* An error occurred */
      return cs;
    if (ncl == scl) return 0;   /* No free cluster */
  }

  res = put_fat(fs, ncl, 0x0FFFFFFF); /* Mark the new cluster "last link" */
  if (res == FR_OK && clst != 0) {
    res = put_fat(fs, clst, ncl); /* Link it to the previous one if needed */
  }
  if (res == FR_OK) {
    fs->last_clust = ncl;     /* Update FSINFO */
    if (fs->free_clust != 0xFFFFFFFF) {
      fs->free_clust--;
      fs->fsi_flag = 1;
    }
  } else {
    ncl = (res == FR_DISK_ERR) ? 0xFFFFFFFF : 1;
  }

  return ncl;   /* Return new cluster number or error code */
}
#endif /* !_FS_READONLY */



/*-----------------------------------------------------------------------*/
/* FAT handling - Convert offset into cluster with link map table        */
/*-----------------------------------------------------------------------*/

#if _USE_FASTSEEK
static
DWORD clmt_clust (  /* <2:Error, >=2:Cluster number */
  FIL* fp,    /* Pointer to the file object */
  DWORD ofs   /* File offset to be converted to cluster# */
)
{
  DWORD cl, ncl, *tbl;


  tbl = fp->cltbl + 1;  /* Top of CLMT */
  cl = ofs / SS(fp->fs) / fp->fs->csize;  /* Cluster order from top of the file */
  for (;;) {
    ncl = *tbl++;     /* Number of cluters in the fragment */
    if (!ncl) return 0;   /* End of table? (error) */
    if (cl < ncl) break;  /* In this fragment? */
    cl -= ncl; tbl++;   /* Next fragment */
  }
  return cl + *tbl; /* Return the cluster number */
}
#endif  /* _USE_FASTSEEK */



/*-----------------------------------------------------------------------*/
/* Directory handling - Set directory index                              */
/*-----------------------------------------------------------------------*/

static
FRESULT dir_sdi (
  DIR *dj,    /* Pointer to directory object */
  WORD idx    /* Directory index number */
)
{
  DWORD clst;
  WORD ic;


  dj->index = idx;
  clst = dj->sclust;
  if (clst == 1 || clst >= dj->fs->n_fatent)  /* Check start cluster range */
    return FR_INT_ERR;
  if (!clst && dj->fs->fs_type == FS_FAT32) /* Replace cluster# 0 with root cluster# if in FAT32 */
    clst = dj->fs->dirbase;

  if (clst == 0) {  /* Static table (root-dir in FAT12/16) */
    dj->clust = clst;
    if (idx >= dj->fs->n_rootdir)   /* Index is out of range */
      return FR_INT_ERR;
    dj->sect = dj->fs->dirbase + idx / (SS(dj->fs) / SZ_DIR); /* Sector# */
  }
  else {        /* Dynamic table (sub-dirs or root-dir in FAT32) */
    ic = SS(dj->fs) / SZ_DIR * dj->fs->csize; /* Entries per cluster */
    while (idx >= ic) { /* Follow cluster chain */
      clst = get_fat(dj->fs, clst);       /* Get next cluster */
      if (clst == 0xFFFFFFFF) return FR_DISK_ERR; /* Disk error */
      if (clst < 2 || clst >= dj->fs->n_fatent) /* Reached to end of table or int error */
        return FR_INT_ERR;
      idx -= ic;
    }
    dj->clust = clst;
    dj->sect = clust2sect(dj->fs, clst) + idx / (SS(dj->fs) / SZ_DIR);  /* Sector# */
  }

  dj->dir = dj->fs->win + (idx % (SS(dj->fs) / SZ_DIR)) * SZ_DIR; /* Ptr to the entry in the sector */

  return FR_OK; /* Seek succeeded */
}




/*-----------------------------------------------------------------------*/
/* Directory handling - Move directory index next                        */
/*-----------------------------------------------------------------------*/

static
FRESULT dir_next (  /* FR_OK:Succeeded, FR_NO_FILE:End of table, FR_DENIED:EOT and could not stretch */
  DIR *dj,    /* Pointer to directory object */
  int stretch   /* 0: Do not stretch table, 1: Stretch table if needed */
)
{
  DWORD clst;
  WORD i;


  stretch = stretch;    /* To suppress warning on read-only cfg. */
  i = dj->index + 1;
  if (!i || !dj->sect)  /* Report EOT when index has reached 65535 */
    return FR_NO_FILE;

  if (!(i % (SS(dj->fs) / SZ_DIR))) { /* Sector changed? */
    dj->sect++;         /* Next sector */

    if (dj->clust == 0) { /* Static table */
      if (i >= dj->fs->n_rootdir) /* Report EOT when end of table */
        return FR_NO_FILE;
    }
    else {          /* Dynamic table */
      if (((i / (SS(dj->fs) / SZ_DIR)) & (dj->fs->csize - 1)) == 0) { /* Cluster changed? */
        clst = get_fat(dj->fs, dj->clust);        /* Get next cluster */
        if (clst <= 1) return FR_INT_ERR;
        if (clst == 0xFFFFFFFF) return FR_DISK_ERR;
        if (clst >= dj->fs->n_fatent) {         /* When it reached end of dynamic table */
#if !_FS_READONLY
          BYTE c;
          if (!stretch) return FR_NO_FILE;      /* When do not stretch, report EOT */
          clst = create_chain(dj->fs, dj->clust);   /* Stretch cluster chain */
          if (clst == 0) return FR_DENIED;      /* No free cluster */
          if (clst == 1) return FR_INT_ERR;
          if (clst == 0xFFFFFFFF) return FR_DISK_ERR;
          /* Clean-up stretched table */
          if (move_window(dj->fs, 0)) return FR_DISK_ERR; /* Flush active window */
          mem_set(dj->fs->win, 0, SS(dj->fs));      /* Clear window buffer */
          dj->fs->winsect = clust2sect(dj->fs, clst); /* Cluster start sector */
          for (c = 0; c < dj->fs->csize; c++) {   /* Fill the new cluster with 0 */
            dj->fs->wflag = 1;
            if (move_window(dj->fs, 0)) return FR_DISK_ERR;
            dj->fs->winsect++;
          }
          dj->fs->winsect -= c;           /* Rewind window address */
#else
          return FR_NO_FILE;      /* Report EOT */
#endif
        }
        dj->clust = clst;       /* Initialize data for new cluster */
        dj->sect = clust2sect(dj->fs, clst);
      }
    }
  }

  dj->index = i;
  dj->dir = dj->fs->win + (i % (SS(dj->fs) / SZ_DIR)) * SZ_DIR;

  return FR_OK;
}




/*-----------------------------------------------------------------------*/
/* LFN handling - Test/Pick/Fit an LFN segment from/to directory entry   */
/*-----------------------------------------------------------------------*/
#if _USE_LFN
static
const BYTE LfnOfs[] = {1,3,5,7,9,14,16,18,20,22,24,28,30};  /* Offset of LFN chars in the directory entry */


static
int cmp_lfn (     /* 1:Matched, 0:Not matched */
  WCHAR *lfnbuf,    /* Pointer to the LFN to be compared */
  BYTE *dir     /* Pointer to the directory entry containing a part of LFN */
)
{
  UINT i, s;
  WCHAR wc, uc;


  i = ((dir[LDIR_Ord] & ~LLE) - 1) * 13;  /* Get offset in the LFN buffer */
  s = 0; wc = 1;
  do {
    uc = LD_WORD(dir+LfnOfs[s]);  /* Pick an LFN character from the entry */
    if (wc) { /* Last char has not been processed */
      wc = ff_wtoupper(uc);   /* Convert it to upper case */
      if (i >= _MAX_LFN || wc != ff_wtoupper(lfnbuf[i++]))  /* Compare it */
        return 0;       /* Not matched */
    } else {
      if (uc != 0xFFFF) return 0; /* Check filler */
    }
  } while (++s < 13);       /* Repeat until all chars in the entry are checked */

  if ((dir[LDIR_Ord] & LLE) && wc && lfnbuf[i]) /* Last segment matched but different length */
    return 0;

  return 1;           /* The part of LFN matched */
}



static
int pick_lfn (      /* 1:Succeeded, 0:Buffer overflow */
  WCHAR *lfnbuf,    /* Pointer to the Unicode-LFN buffer */
  BYTE *dir     /* Pointer to the directory entry */
)
{
  UINT i, s;
  WCHAR wc, uc;


  i = ((dir[LDIR_Ord] & 0x3F) - 1) * 13;  /* Offset in the LFN buffer */

  s = 0; wc = 1;
  do {
    uc = LD_WORD(dir+LfnOfs[s]);    /* Pick an LFN character from the entry */
    if (wc) { /* Last char has not been processed */
      if (i >= _MAX_LFN) return 0;  /* Buffer overflow? */
      lfnbuf[i++] = wc = uc;      /* Store it */
    } else {
      if (uc != 0xFFFF) return 0;   /* Check filler */
    }
  } while (++s < 13);           /* Read all character in the entry */

  if (dir[LDIR_Ord] & LLE) {        /* Put terminator if it is the last LFN part */
    if (i >= _MAX_LFN) return 0;    /* Buffer overflow? */
    lfnbuf[i] = 0;
  }

  return 1;
}


#if !_FS_READONLY
static
void fit_lfn (
  const WCHAR *lfnbuf,  /* Pointer to the LFN buffer */
  BYTE *dir,        /* Pointer to the directory entry */
  BYTE ord,       /* LFN order (1-20) */
  BYTE sum        /* SFN sum */
)
{
  UINT i, s;
  WCHAR wc;


  dir[LDIR_Chksum] = sum;     /* Set check sum */
  dir[LDIR_Attr] = AM_LFN;    /* Set attribute. LFN entry */
  dir[LDIR_Type] = 0;
  ST_WORD(dir+LDIR_FstClusLO, 0);

  i = (ord - 1) * 13;       /* Get offset in the LFN buffer */
  s = wc = 0;
  do {
    if (wc != 0xFFFF) wc = lfnbuf[i++]; /* Get an effective char */
    ST_WORD(dir+LfnOfs[s], wc); /* Put it */
    if (!wc) wc = 0xFFFF;   /* Padding chars following last char */
  } while (++s < 13);
  if (wc == 0xFFFF || !lfnbuf[i]) ord |= LLE; /* Bottom LFN part is the start of LFN sequence */
  dir[LDIR_Ord] = ord;      /* Set the LFN order */
}

#endif
#endif



/*-----------------------------------------------------------------------*/
/* Create numbered name                                                  */
/*-----------------------------------------------------------------------*/
#if _USE_LFN
static void gen_numname (
  BYTE *dst,      /* Pointer to generated SFN */
  const BYTE *src,  /* Pointer to source SFN to be modified */
  const WCHAR *lfn, /* Pointer to LFN */
  WORD seq      /* Sequence number */
)
{
  BYTE ns[8], c;
  UINT i, j;


  mem_cpy(dst, src, 11);

  if (seq > 5) {  /* On many collisions, generate a hash number instead of sequential number */
    do seq = (seq >> 1) + (seq << 15) + (WORD)*lfn++; while (*lfn);
  }

  /* itoa (hexdecimal) */
  i = 7;
  do {
    c = (seq % 16) + '0';
    if (c > '9') c += 7;
    ns[i--] = c;
    seq /= 16;
  } while (seq);
  ns[i] = '~';

  /* Append the number */
  for (j = 0; j < i && dst[j] != ' '; j++) {
    if (IsDBCS1(dst[j])) {
      if (j == i - 1) break;
      j++;
    }
  }
  do {
    dst[j++] = (i < 8) ? ns[i++] : ' ';
  } while (j < 8);
}
#endif




/*-----------------------------------------------------------------------*/
/* Calculate sum of an SFN                                               */
/*-----------------------------------------------------------------------*/
#if _USE_LFN
static
BYTE sum_sfn (
  const BYTE *dir   /* Ptr to directory entry */
)
{
  BYTE sum = 0;
  UINT n = 11;

  do sum = (sum >> 1) + (sum << 7) + *dir++; while (--n);
  return sum;
}
#endif




/*-----------------------------------------------------------------------*/
/* Directory handling - Find an object in the directory                  */
/*-----------------------------------------------------------------------*/

static
FRESULT dir_find (
  DIR *dj     /* Pointer to the directory object linked to the file name */
)
{
  FRESULT res;
  BYTE c, *dir;
#if _USE_LFN
  BYTE a, ord, sum;
#endif

  res = dir_sdi(dj, 0);     /* Rewind directory object */
  if (res != FR_OK) return res;

#if _USE_LFN
  ord = sum = 0xFF;
#endif
  do {
    res = move_window(dj->fs, dj->sect);
    if (res != FR_OK) break;
    dir = dj->dir;          /* Ptr to the directory entry of current index */
    c = dir[DIR_Name];
    if (c == 0) { res = FR_NO_FILE; break; }  /* Reached to end of table */
#if _USE_LFN  /* LFN configuration */
    a = dir[DIR_Attr] & AM_MASK;
    if (c == DDE || ((a & AM_VOL) && a != AM_LFN)) {  /* An entry without valid data */
      ord = 0xFF;
    } else {
      if (a == AM_LFN) {      /* An LFN entry is found */
        if (dj->lfn) {
          if (c & LLE) {    /* Is it start of LFN sequence? */
            sum = dir[LDIR_Chksum];
            c &= ~LLE; ord = c; /* LFN start order */
            dj->lfn_idx = dj->index;
          }
          /* Check validity of the LFN entry and compare it with given name */
          ord = (c == ord && sum == dir[LDIR_Chksum] && cmp_lfn(dj->lfn, dir)) ? ord - 1 : 0xFF;
        }
      } else {          /* An SFN entry is found */
        if (!ord && sum == sum_sfn(dir)) break; /* LFN matched? */
        ord = 0xFF; dj->lfn_idx = 0xFFFF; /* Reset LFN sequence */
        if (!(dj->fn[NS] & NS_LOSS) && !mem_cmp(dir, dj->fn, 11)) break;  /* SFN matched? */
      }
    }
#else   /* Non LFN configuration */
    if (!(dir[DIR_Attr] & AM_VOL) && !mem_cmp(dir, dj->fn, 11)) /* Is it a valid entry? */
      break;
#endif
    res = dir_next(dj, 0);    /* Next entry */
  } while (res == FR_OK);

  return res;
}




/*-----------------------------------------------------------------------*/
/* Read an object from the directory                                     */
/*-----------------------------------------------------------------------*/
#if _FS_MINIMIZE <= 1
static
FRESULT dir_read (
  DIR *dj     /* Pointer to the directory object that pointing the entry to be read */
)
{
  FRESULT res;
  BYTE c, *dir;
#if _USE_LFN
  BYTE a, ord = 0xFF, sum = 0xFF;
#endif

  res = FR_NO_FILE;
  while (dj->sect) {
    res = move_window(dj->fs, dj->sect);
    if (res != FR_OK) break;
    dir = dj->dir;          /* Ptr to the directory entry of current index */
    c = dir[DIR_Name];
    if (c == 0) { res = FR_NO_FILE; break; }  /* Reached to end of table */
#if _USE_LFN  /* LFN configuration */
    a = dir[DIR_Attr] & AM_MASK;
    if (c == DDE || (!_FS_RPATH && c == '.') || ((a & AM_VOL) && a != AM_LFN)) {  /* An entry without valid data */
      ord = 0xFF;
    } else {
      if (a == AM_LFN) {      /* An LFN entry is found */
        if (c & LLE) {      /* Is it start of LFN sequence? */
          sum = dir[LDIR_Chksum];
          c &= ~LLE; ord = c;
          dj->lfn_idx = dj->index;
        }
        /* Check LFN validity and capture it */
        ord = (c == ord && sum == dir[LDIR_Chksum] && pick_lfn(dj->lfn, dir)) ? ord - 1 : 0xFF;
      } else {          /* An SFN entry is found */
        if (ord || sum != sum_sfn(dir)) /* Is there a valid LFN? */
          dj->lfn_idx = 0xFFFF;   /* It has no LFN. */
        break;
      }
    }
#else   /* Non LFN configuration */
    if (c != DDE && (_FS_RPATH || c != '.') && !(dir[DIR_Attr] & AM_VOL)) /* Is it a valid entry? */
      break;
#endif
    res = dir_next(dj, 0);        /* Next entry */
    if (res != FR_OK) break;
  }

  if (res != FR_OK) dj->sect = 0;

  return res;
}
#endif



/*-----------------------------------------------------------------------*/
/* Register an object to the directory                                   */
/*-----------------------------------------------------------------------*/
#if !_FS_READONLY
static
FRESULT dir_register (  /* FR_OK:Successful, FR_DENIED:No free entry or too many SFN collision, FR_DISK_ERR:Disk error */
  DIR *dj       /* Target directory with object name to be created */
)
{
  FRESULT res;
  BYTE c, *dir;
#if _USE_LFN  /* LFN configuration */
  WORD n, ne, is;
  BYTE sn[12], *fn, sum;
  WCHAR *lfn;


  fn = dj->fn; lfn = dj->lfn;
  mem_cpy(sn, fn, 12);

  if (_FS_RPATH && (sn[NS] & NS_DOT))   /* Cannot create dot entry */
    return FR_INVALID_NAME;

  if (sn[NS] & NS_LOSS) {     /* When LFN is out of 8.3 format, generate a numbered name */
    fn[NS] = 0; dj->lfn = 0;      /* Find only SFN */
    for (n = 1; n < 100; n++) {
      gen_numname(fn, sn, lfn, n);  /* Generate a numbered name */
      res = dir_find(dj);       /* Check if the name collides with existing SFN */
      if (res != FR_OK) break;
    }
    if (n == 100) return FR_DENIED;   /* Abort if too many collisions */
    if (res != FR_NO_FILE) return res;  /* Abort if the result is other than 'not collided' */
    fn[NS] = sn[NS]; dj->lfn = lfn;
  }

  if (sn[NS] & NS_LFN) {      /* When LFN is to be created, reserve an SFN + LFN entries. */
    for (ne = 0; lfn[ne]; ne++) ;
    ne = (ne + 25) / 13;
  } else {            /* Otherwise reserve only an SFN entry. */
    ne = 1;
  }

  /* Reserve contiguous entries */
  res = dir_sdi(dj, 0);
  if (res != FR_OK) return res;
  n = is = 0;
  do {
    res = move_window(dj->fs, dj->sect);
    if (res != FR_OK) break;
    c = *dj->dir;       /* Check the entry status */
    if (c == DDE || c == 0) { /* Is it a blank entry? */
      if (n == 0) is = dj->index; /* First index of the contiguous entry */
      if (++n == ne) break; /* A contiguous entry that required count is found */
    } else {
      n = 0;          /* Not a blank entry. Restart to search */
    }
    res = dir_next(dj, 1);    /* Next entry with table stretch */
  } while (res == FR_OK);

  if (res == FR_OK && ne > 1) { /* Initialize LFN entry if needed */
    res = dir_sdi(dj, is);
    if (res == FR_OK) {
      sum = sum_sfn(dj->fn);  /* Sum of the SFN tied to the LFN */
      ne--;
      do {          /* Store LFN entries in bottom first */
        res = move_window(dj->fs, dj->sect);
        if (res != FR_OK) break;
        fit_lfn(dj->lfn, dj->dir, (BYTE)ne, sum);
        dj->fs->wflag = 1;
        res = dir_next(dj, 0);  /* Next entry */
      } while (res == FR_OK && --ne);
    }
  }

#else /* Non LFN configuration */
  res = dir_sdi(dj, 0);
  if (res == FR_OK) {
    do {  /* Find a blank entry for the SFN */
      res = move_window(dj->fs, dj->sect);
      if (res != FR_OK) break;
      c = *dj->dir;
      if (c == DDE || c == 0) break;  /* Is it a blank entry? */
      res = dir_next(dj, 1);      /* Next entry with table stretch */
    } while (res == FR_OK);
  }
#endif

  if (res == FR_OK) {   /* Initialize the SFN entry */
    res = move_window(dj->fs, dj->sect);
    if (res == FR_OK) {
      dir = dj->dir;
      mem_set(dir, 0, SZ_DIR);  /* Clean the entry */
      mem_cpy(dir, dj->fn, 11); /* Put SFN */
#if _USE_LFN
      dir[DIR_NTres] = *(dj->fn+NS) & (NS_BODY | NS_EXT); /* Put NT flag */
#endif
      dj->fs->wflag = 1;
    }
  }

  return res;
}
#endif /* !_FS_READONLY */




/*-----------------------------------------------------------------------*/
/* Remove an object from the directory                                   */
/*-----------------------------------------------------------------------*/
#if !_FS_READONLY && !_FS_MINIMIZE
static
FRESULT dir_remove (  /* FR_OK: Successful, FR_DISK_ERR: A disk error */
  DIR *dj       /* Directory object pointing the entry to be removed */
)
{
  FRESULT res;
#if _USE_LFN  /* LFN configuration */
  WORD i;

  i = dj->index;  /* SFN index */
  res = dir_sdi(dj, (WORD)((dj->lfn_idx == 0xFFFF) ? i : dj->lfn_idx)); /* Goto the SFN or top of the LFN entries */
  if (res == FR_OK) {
    do {
      res = move_window(dj->fs, dj->sect);
      if (res != FR_OK) break;
      *dj->dir = DDE;     /* Mark the entry "deleted" */
      dj->fs->wflag = 1;
      if (dj->index >= i) break;  /* When reached SFN, all entries of the object has been deleted. */
      res = dir_next(dj, 0);    /* Next entry */
    } while (res == FR_OK);
    if (res == FR_NO_FILE) res = FR_INT_ERR;
  }

#else     /* Non LFN configuration */
  res = dir_sdi(dj, dj->index);
  if (res == FR_OK) {
    res = move_window(dj->fs, dj->sect);
    if (res == FR_OK) {
      *dj->dir = DDE;     /* Mark the entry "deleted" */
      dj->fs->wflag = 1;
    }
  }
#endif

  return res;
}
#endif /* !_FS_READONLY */




/*-----------------------------------------------------------------------*/
/* Pick a segment and create the object name in directory form           */
/*-----------------------------------------------------------------------*/

static
FRESULT create_name (
  DIR *dj,      /* Pointer to the directory object */
  const TCHAR **path  /* Pointer to pointer to the segment in the path string */
)
{
#ifdef _EXCVT
  static const BYTE excvt[] = _EXCVT; /* Upper conversion table for extended chars */
#endif

#if _USE_LFN  /* LFN configuration */
  BYTE b, cf;
  WCHAR w, *lfn;
  UINT i, ni, si, di;
  const TCHAR *p;

  /* Create LFN in Unicode */
  for (p = *path; *p == '/' || *p == '\\'; p++) ; /* Strip duplicated separator */
  lfn = dj->lfn;
  si = di = 0;
  for (;;) {
    w = p[si++];          /* Get a character */
    if (w < ' ' || w == '/' || w == '\\') break;  /* Break on end of segment */
    if (di >= _MAX_LFN)       /* Reject too long name */
      return FR_INVALID_NAME;
#if !_LFN_UNICODE
    w &= 0xFF;
    if (IsDBCS1(w)) {       /* Check if it is a DBC 1st byte (always false on SBCS cfg) */
      b = (BYTE)p[si++];      /* Get 2nd byte */
      if (!IsDBCS2(b))
        return FR_INVALID_NAME; /* Reject invalid sequence */
      w = (w << 8) + b;     /* Create a DBC */
    }
    w = ff_convert(w, 1);     /* Convert ANSI/OEM to Unicode */
    if (!w) return FR_INVALID_NAME; /* Reject invalid code */
#endif
    if (w < 0x80 && chk_chr("\"*:<>\?|\x7F", w)) /* Reject illegal chars for LFN */
      return FR_INVALID_NAME;
    lfn[di++] = w;          /* Store the Unicode char */
  }
  *path = &p[si];           /* Return pointer to the next segment */
  cf = (w < ' ') ? NS_LAST : 0;   /* Set last segment flag if end of path */
#if _FS_RPATH
  if ((di == 1 && lfn[di-1] == '.') || /* Is this a dot entry? */
    (di == 2 && lfn[di-1] == '.' && lfn[di-2] == '.')) {
    lfn[di] = 0;
    for (i = 0; i < 11; i++)
      dj->fn[i] = (i < di) ? '.' : ' ';
    dj->fn[i] = cf | NS_DOT;    /* This is a dot entry */
    return FR_OK;
  }
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
